akkdong/Vario-STM32/case/Button.png

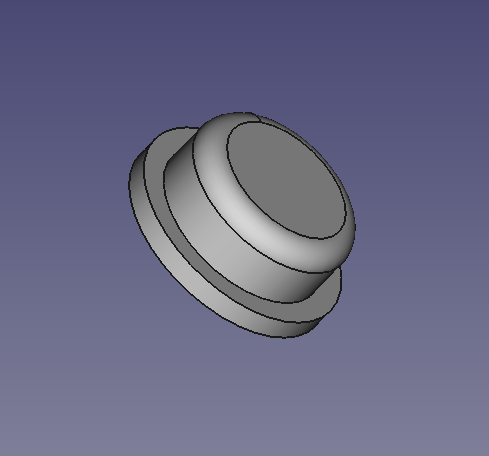
case/Button.png
