akkdong/Vario-STM32/case/case-bottom.png

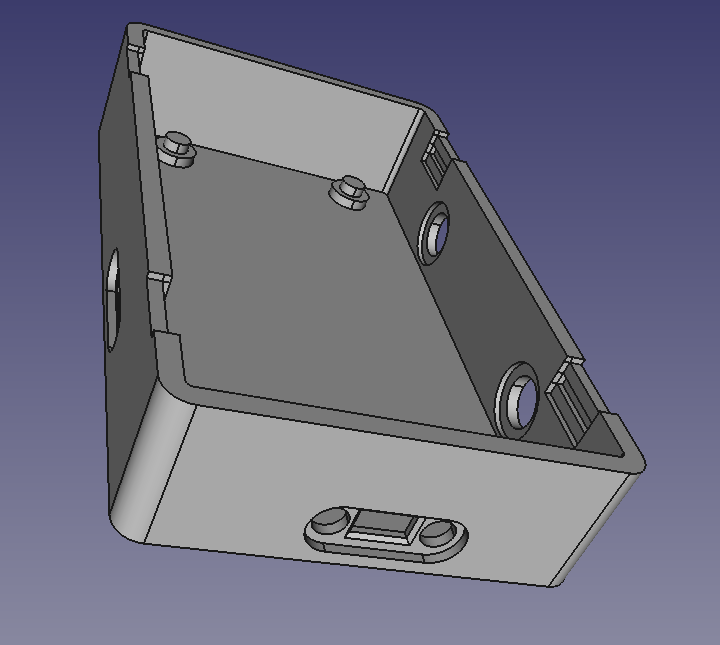
case/case-bottom.png
