akkdong/Vario-STM32/case/case-top.png

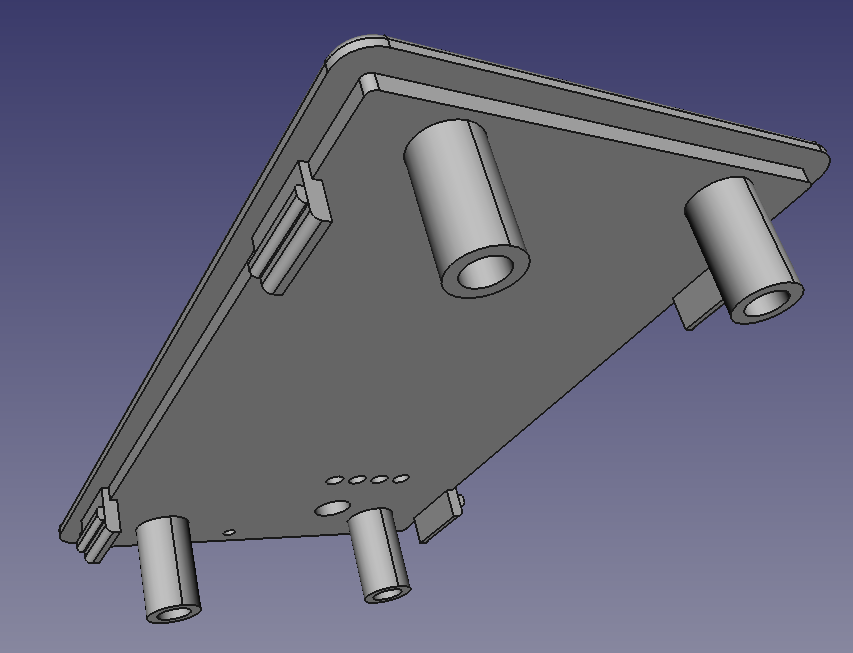
case/case-top.png
