akkdong/Vario-STM32/doc/auto power off - 2.jpg

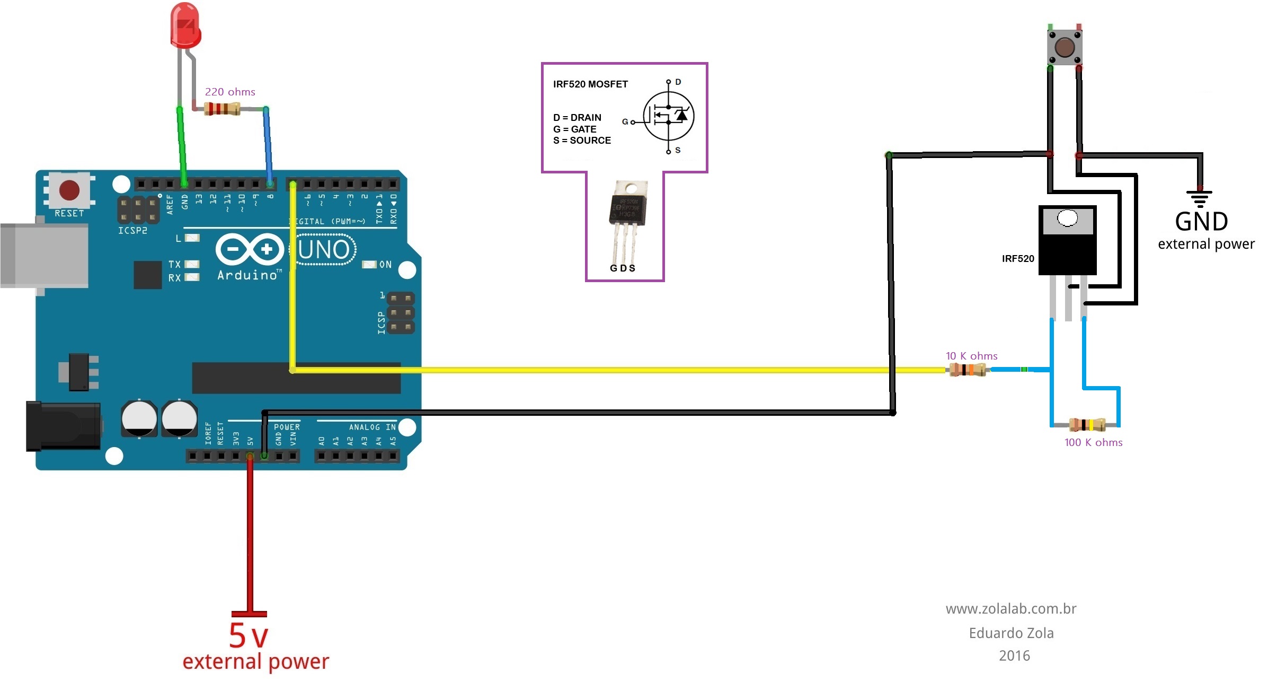
doc/auto power off - 2.jpg
