akkdong/Vario-STM32/doc/auto power off - 3.jpg

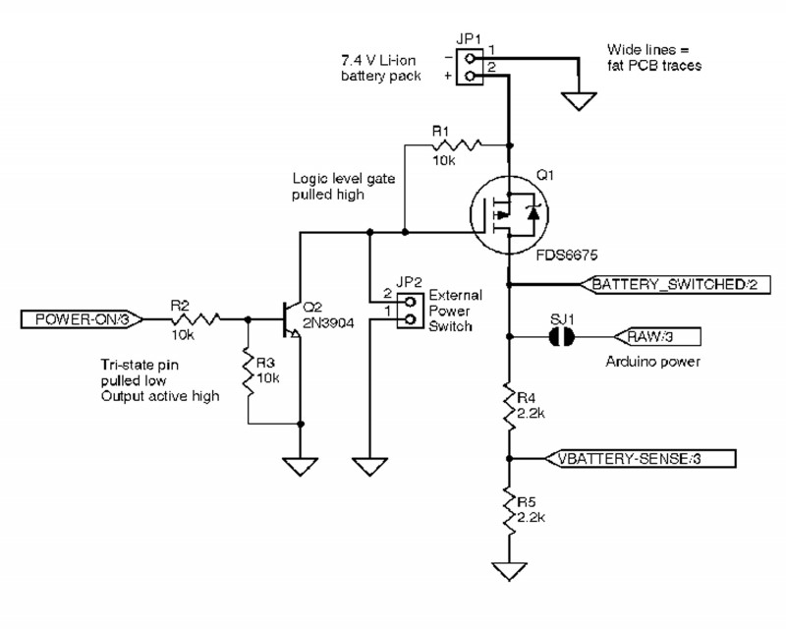
doc/auto power off - 3.jpg
