akkdong/Vario-STM32/doc/FGPMMOPA6C.jpg

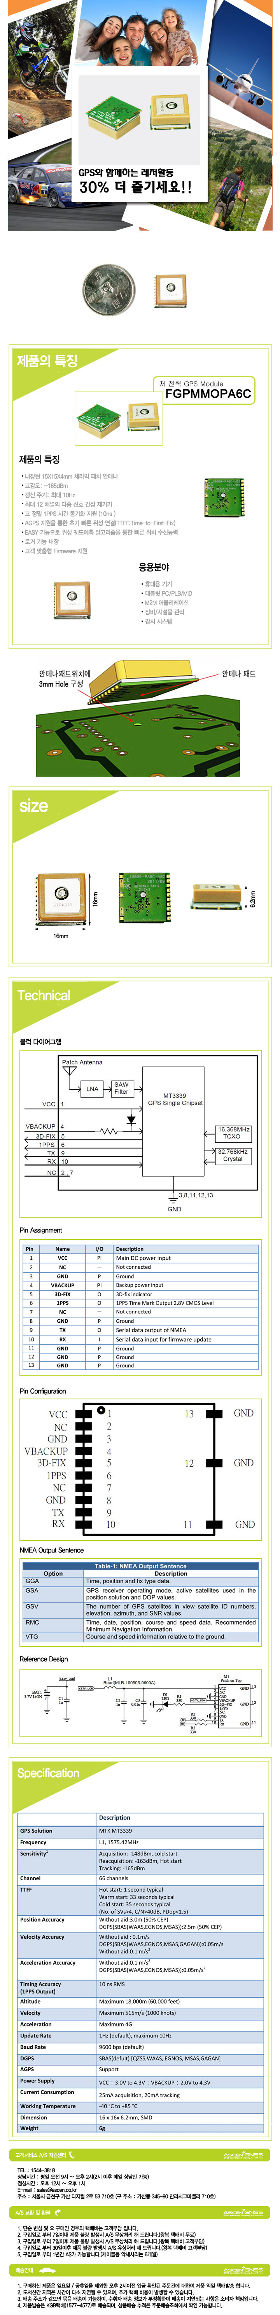
doc/FGPMMOPA6C.jpg
