akkdong/Vario-STM32/doc/in-rush-limited-push-button-on-off-toggle-power-switch-circuit.png

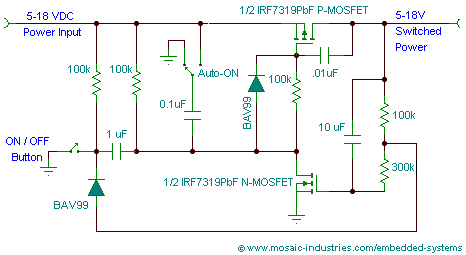
doc/in-rush-limited-push-button-on-off-toggle-power-switch-circuit.png
