akkdong/Vario-STM32/doc/latching-high-side-toggle-switch-circuit-for-capacitive-loads.png

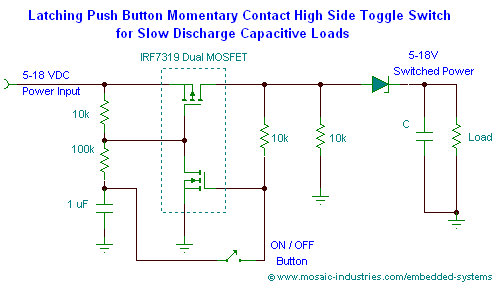
doc/latching-high-side-toggle-switch-circuit-for-capacitive-loads.png
