akkdong/Vario-STM32/doc/LTC2950-1 - Push Button OnOff Controller.png

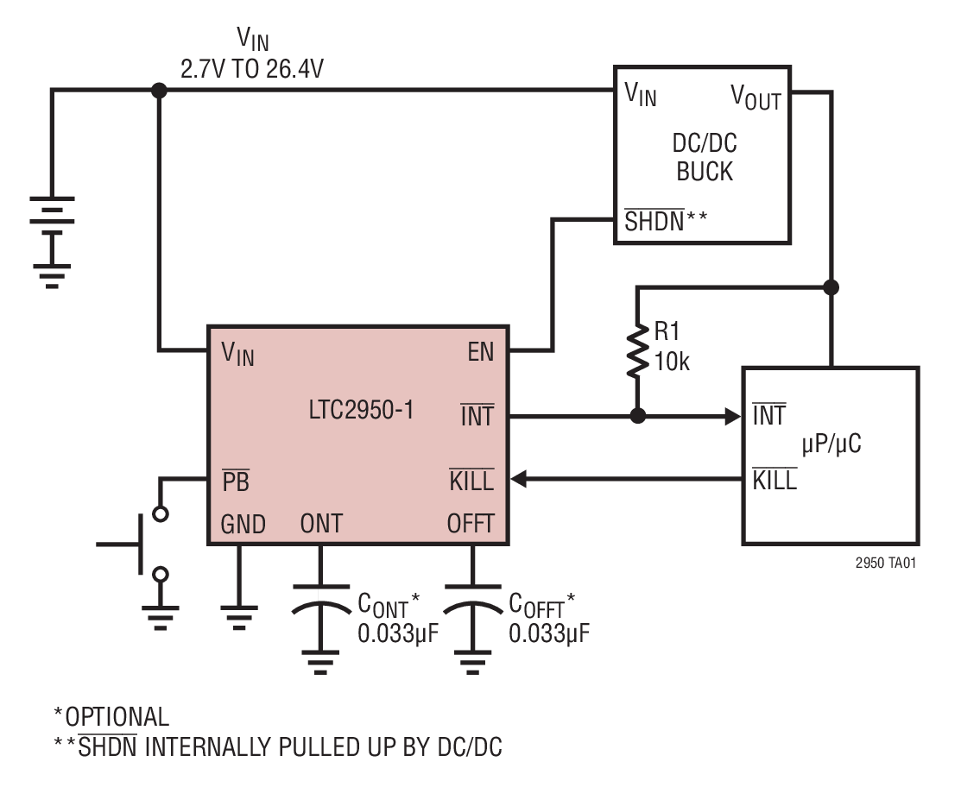
doc/LTC2950-1 - Push Button OnOff Controller.png
