akkdong/Vario-STM32/doc/LTC2953 - Push Button OnOff Controller with Voltage Monitoring.png

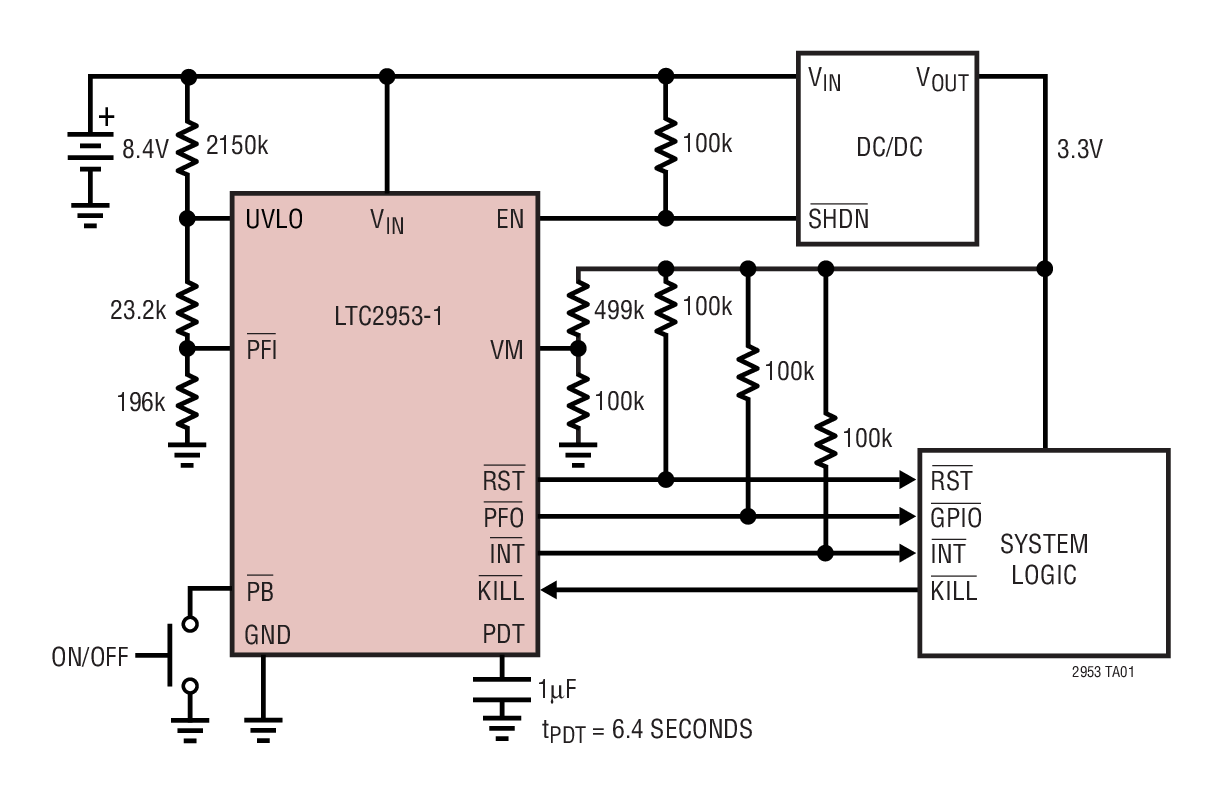
doc/LTC2953 - Push Button OnOff Controller with Voltage Monitoring.png
