akkdong/Vario-STM32/doc/pcb/pcb-bottom-rev2.png

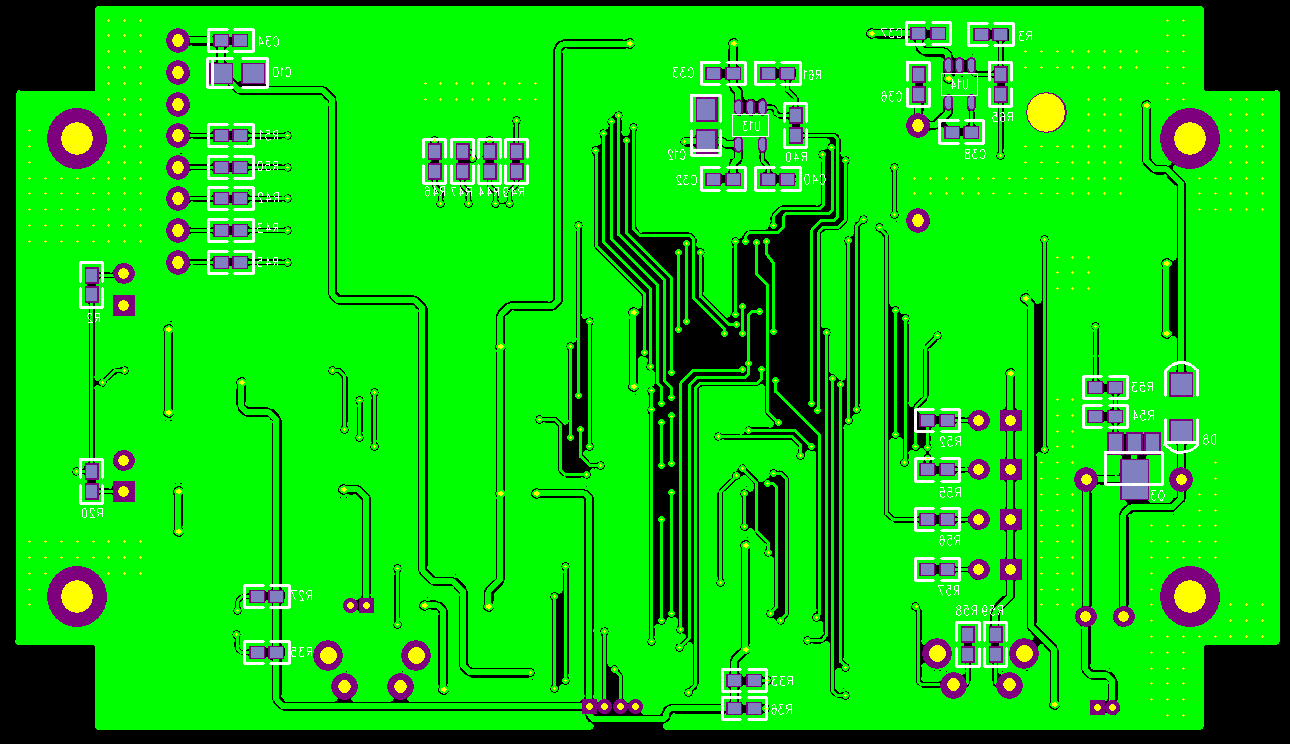
doc/pcb/pcb-bottom-rev2.png
