akkdong/Vario-STM32/doc/pcb/pcb-bottom.png

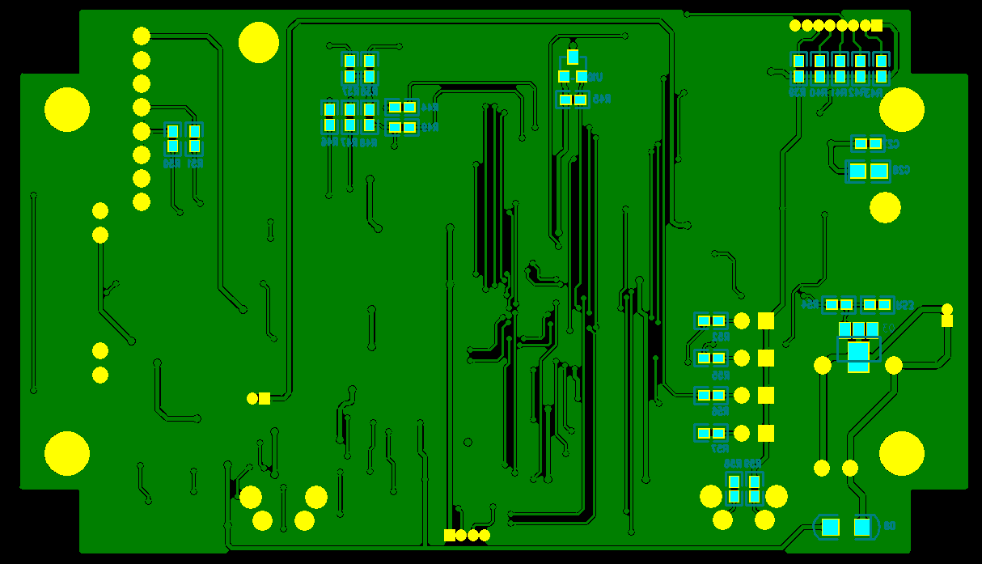
doc/pcb/pcb-bottom.png
