akkdong/Vario-STM32/doc/pcb/pcb-top.png

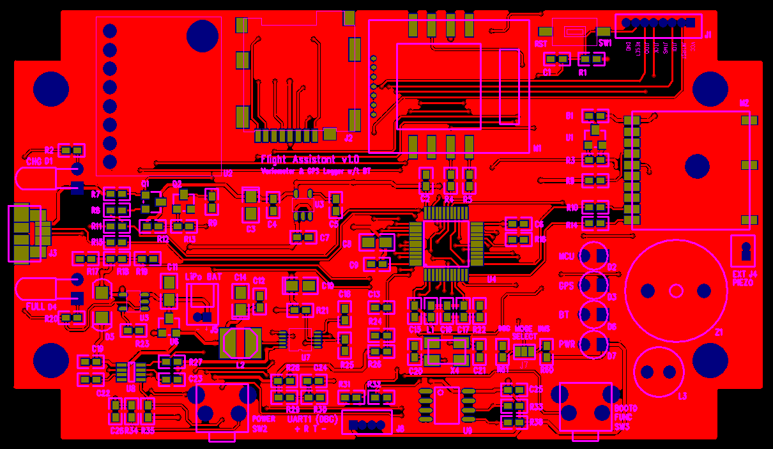
doc/pcb/pcb-top.png
