akkdong/Vario-STM32/doc/piezo/alarm-module.png

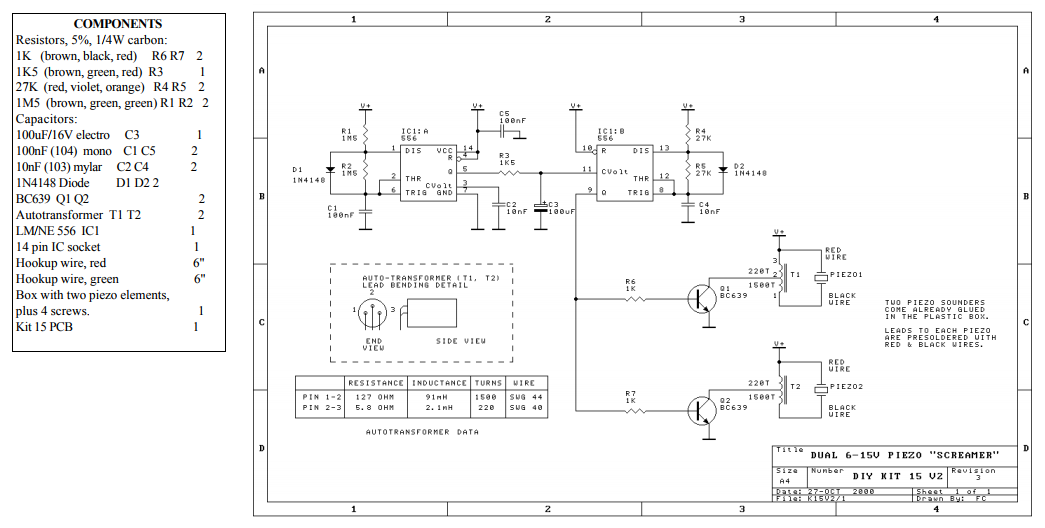
doc/piezo/alarm-module.png
