akkdong/Vario-STM32/doc/piezo/Dual Piezo Driver.png

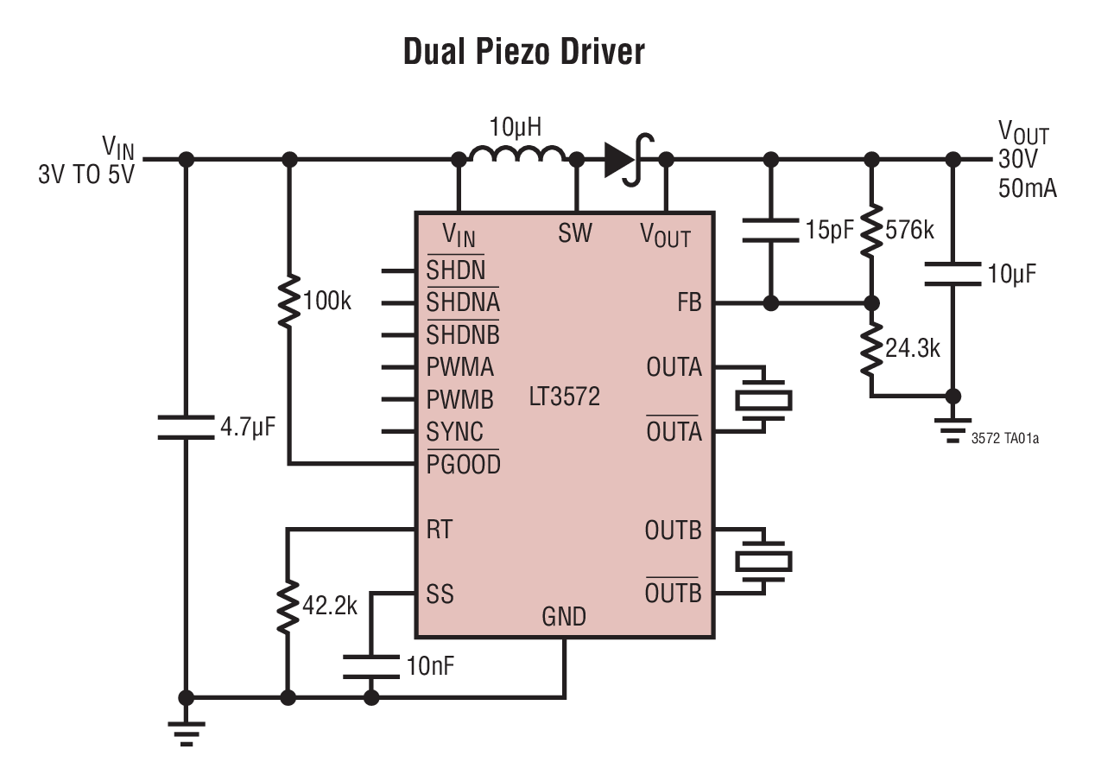
doc/piezo/Dual Piezo Driver.png
