akkdong/Vario-STM32/doc/piezo/FEFHRLSHNM44L13.MEDIUM.jpg

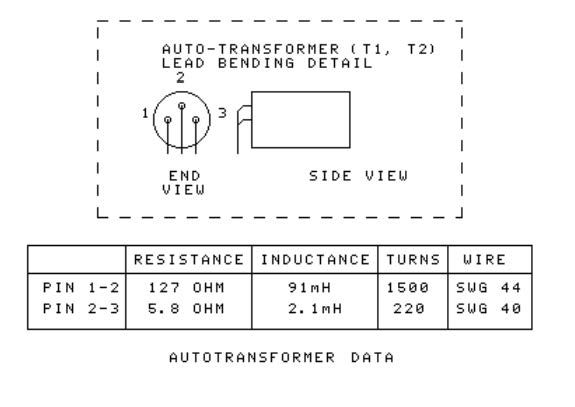
doc/piezo/FEFHRLSHNM44L13.MEDIUM.jpg
