akkdong/Vario-STM32/doc/piezo/FS6PPDVHNM44D6V.MEDIUM.jpg

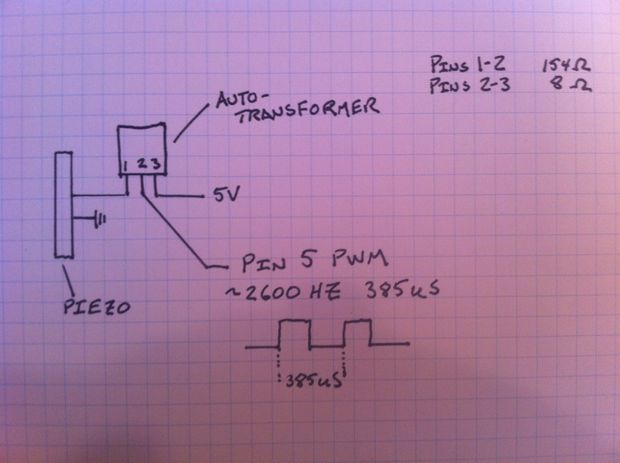
doc/piezo/FS6PPDVHNM44D6V.MEDIUM.jpg
