akkdong/Vario-STM32/doc/piezo/sweeping tone alarm beeper.jpg

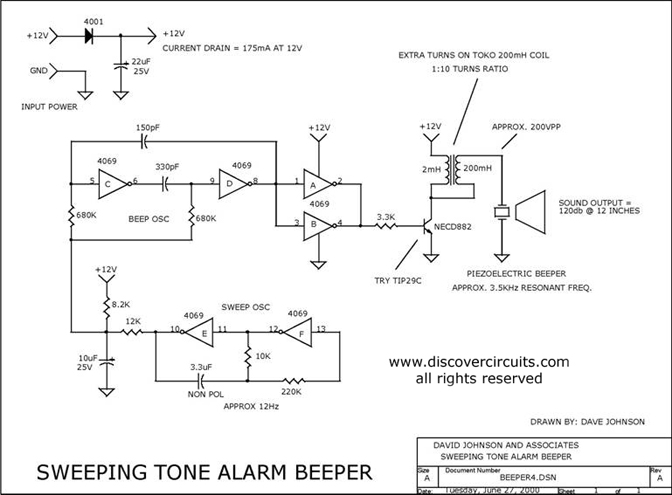
doc/piezo/sweeping tone alarm beeper.jpg
