akkdong/Vario-STM32/case/Sample-Case.FCStd

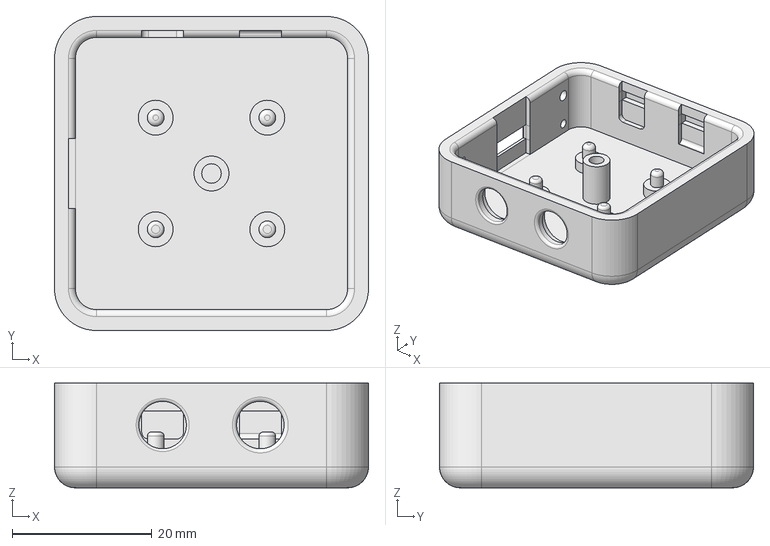
[picture p39: CAD file, 2018-11-01]
case/Sample-Case.FCStd
45.0 x 45.0 x 15.0 mm
