akkdong/Vario-STM32/case/Case-Button.stl

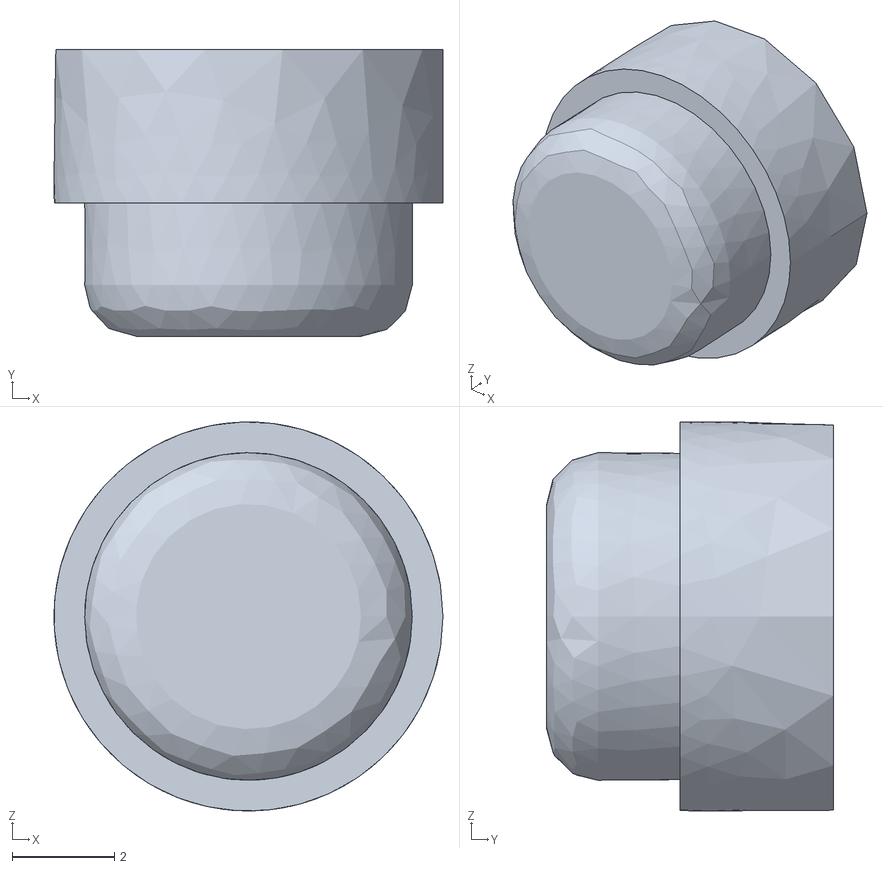
[picture p40: CAD file, 2018-10-25]
case/Case-Button.stl
7.60 x 5.60 x 7.60
