akkdong/Vario-STM32/case/Case-Top-2.FCStd

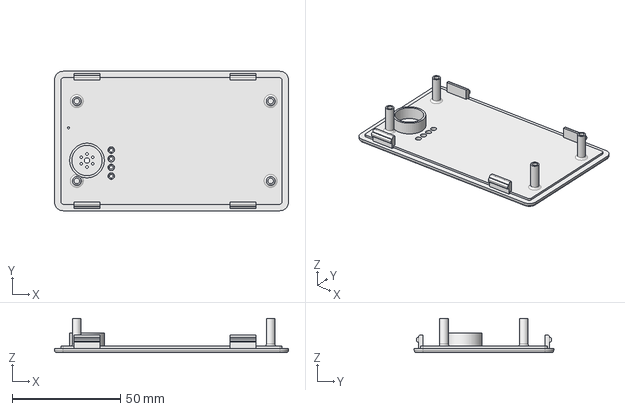
[picture p41: CAD file, 2018-10-23]
case/Case-Top-2.FCStd
108.0 x 64.4 x 15.8 mm
