akkdong/Vario-STM32/case/Case-Bottom-2.FCStd

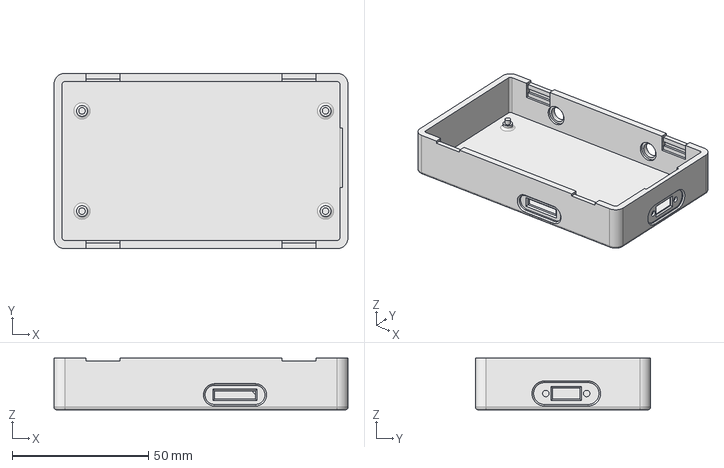
[picture p42: CAD file, 2018-10-23]
case/Case-Bottom-2.FCStd
108.0 x 64.4 x 19.0 mm
