akkdong/Vario-STM32/case/Button.FCStd

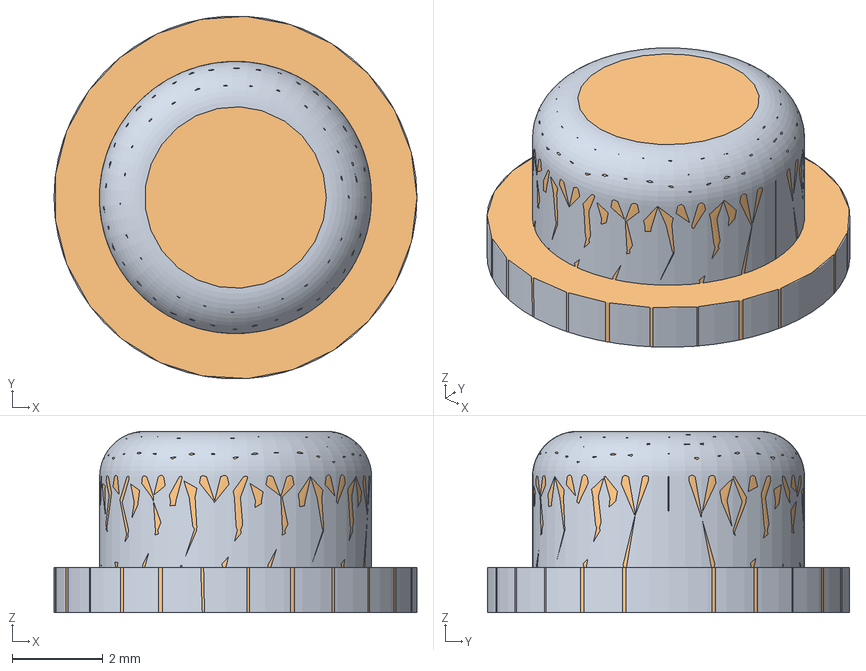
[picture p43: CAD file, 2018-10-23]
case/Button.FCStd
8.00 x 7.99 x 4.00 mm
Pocket (Meshed)
