akkdong/Vario-STM32/case/Case-Bottom.FCStd

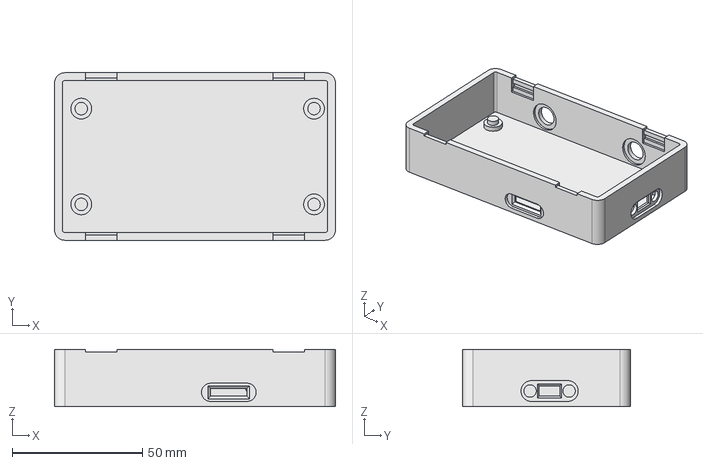
[picture p44: CAD file, 2018-10-21]
case/Case-Bottom.FCStd
108.0 x 64.4 x 22.0 mm
