akkdong/Vario-STM32/doc/battery voltage measure example.jpg

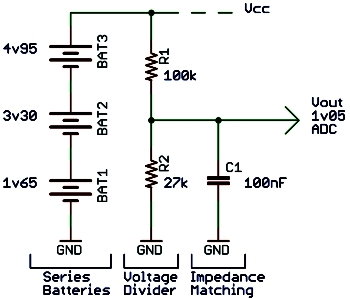
doc/battery voltage measure example.jpg
