akkdong/Vario-STM32/pads/Variometer-STM32-Rev2.pdf

D

6 | 5 | 4 | 3 | 2 | 1

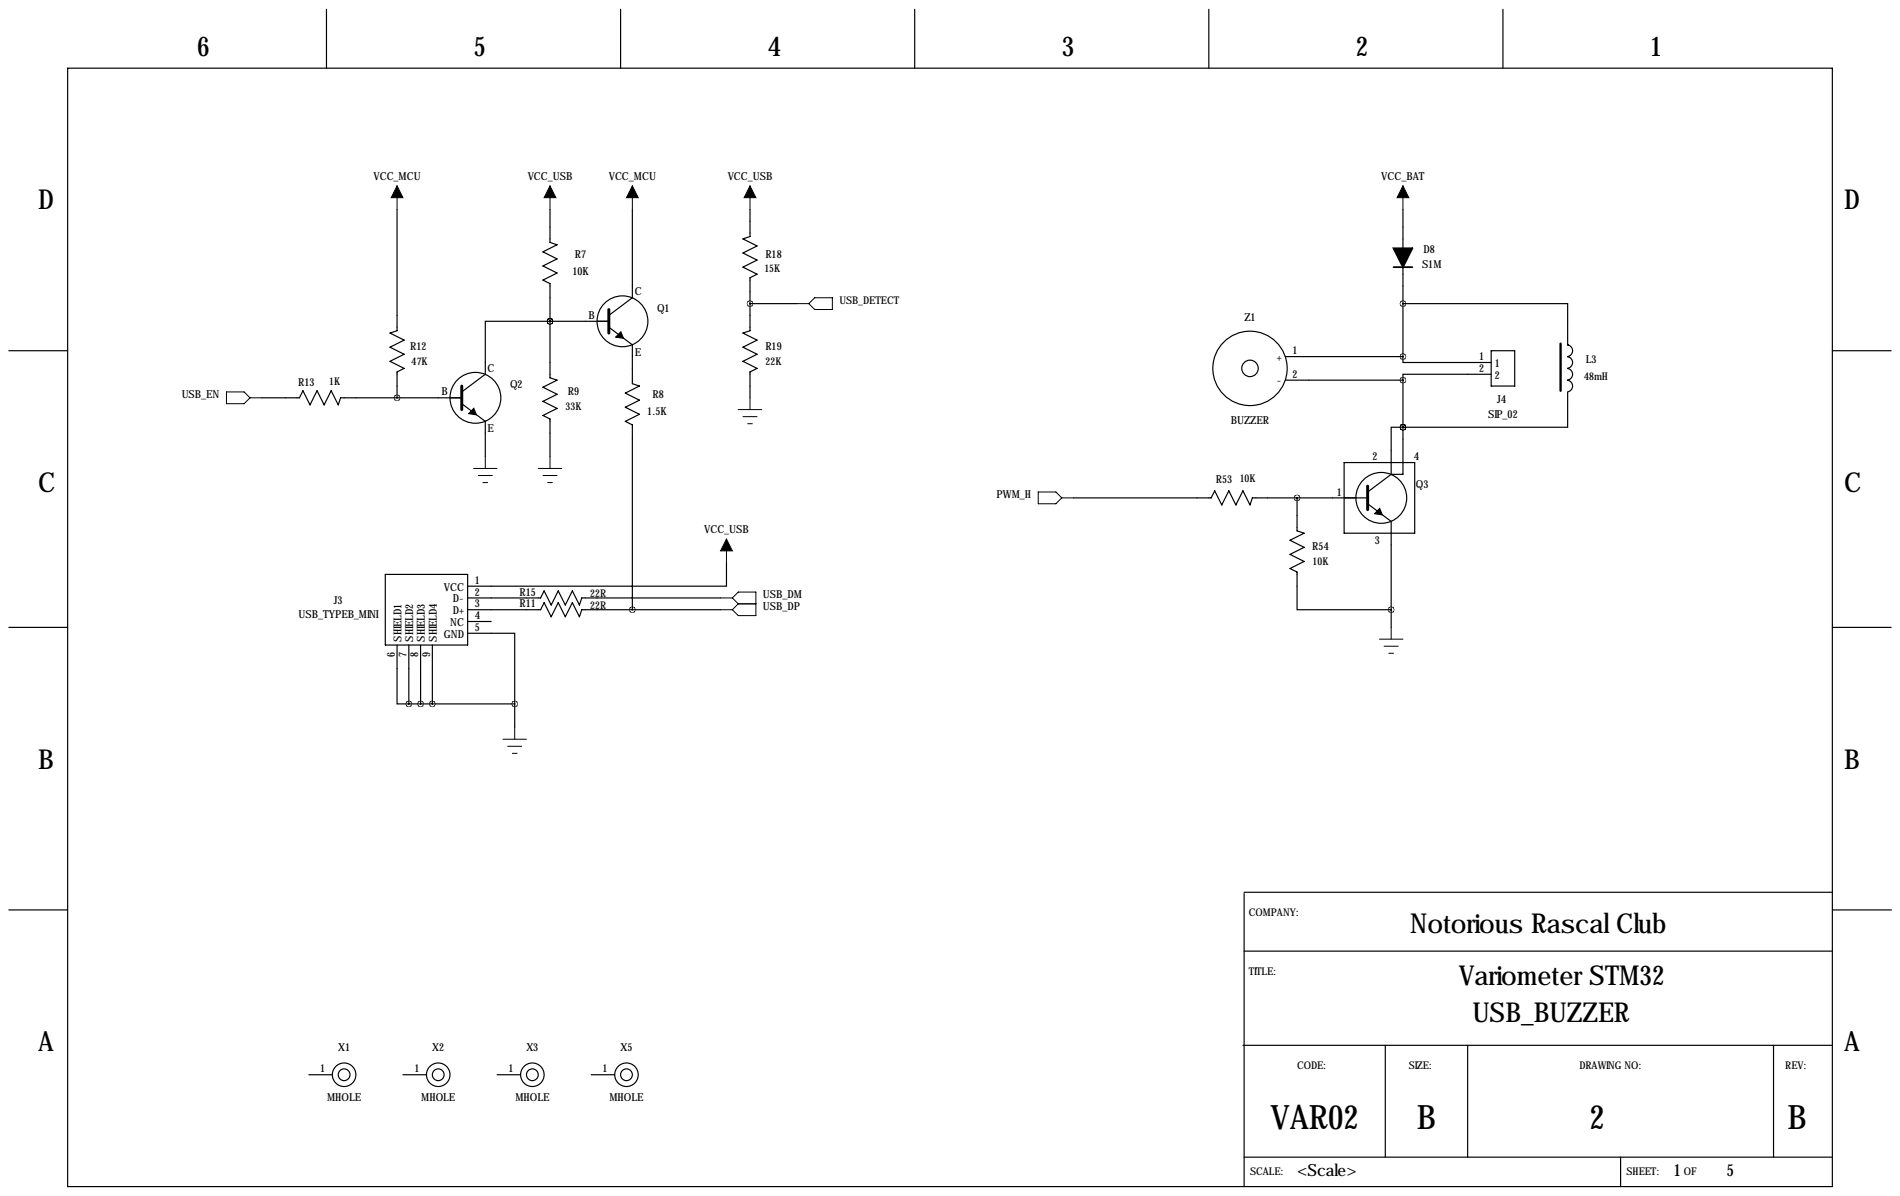
[picture p58: page 1]

CODE: VAR02 | SIZE: B | DRAWING NO: 2 | REV: B

<Scale> SCALE: | 1 5 SHEET: OF

D

D

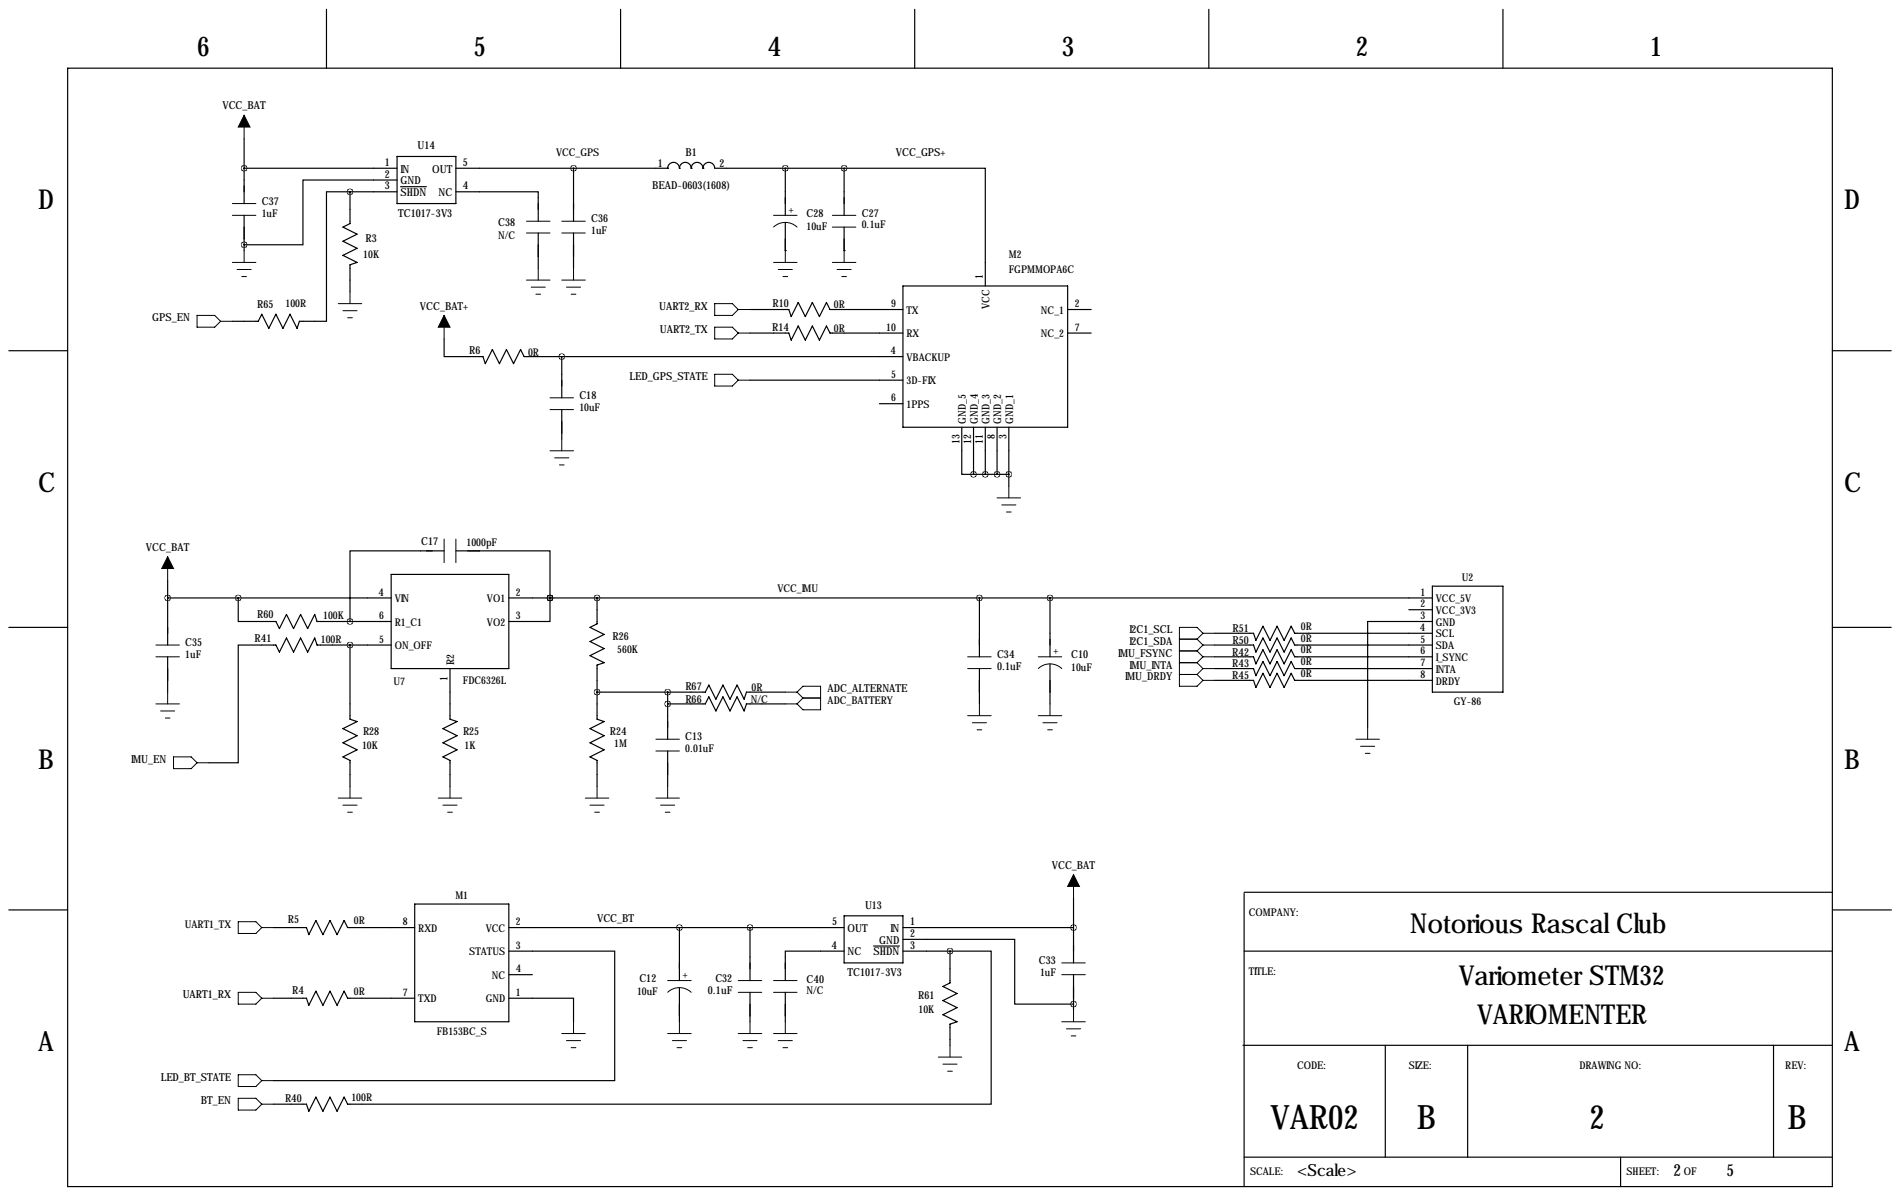
[picture p59: page 2]

CODE: VAR02 | SIZE: B | DRAWING NO: 2 | REV: B

<Scale> | 2 5

D

D

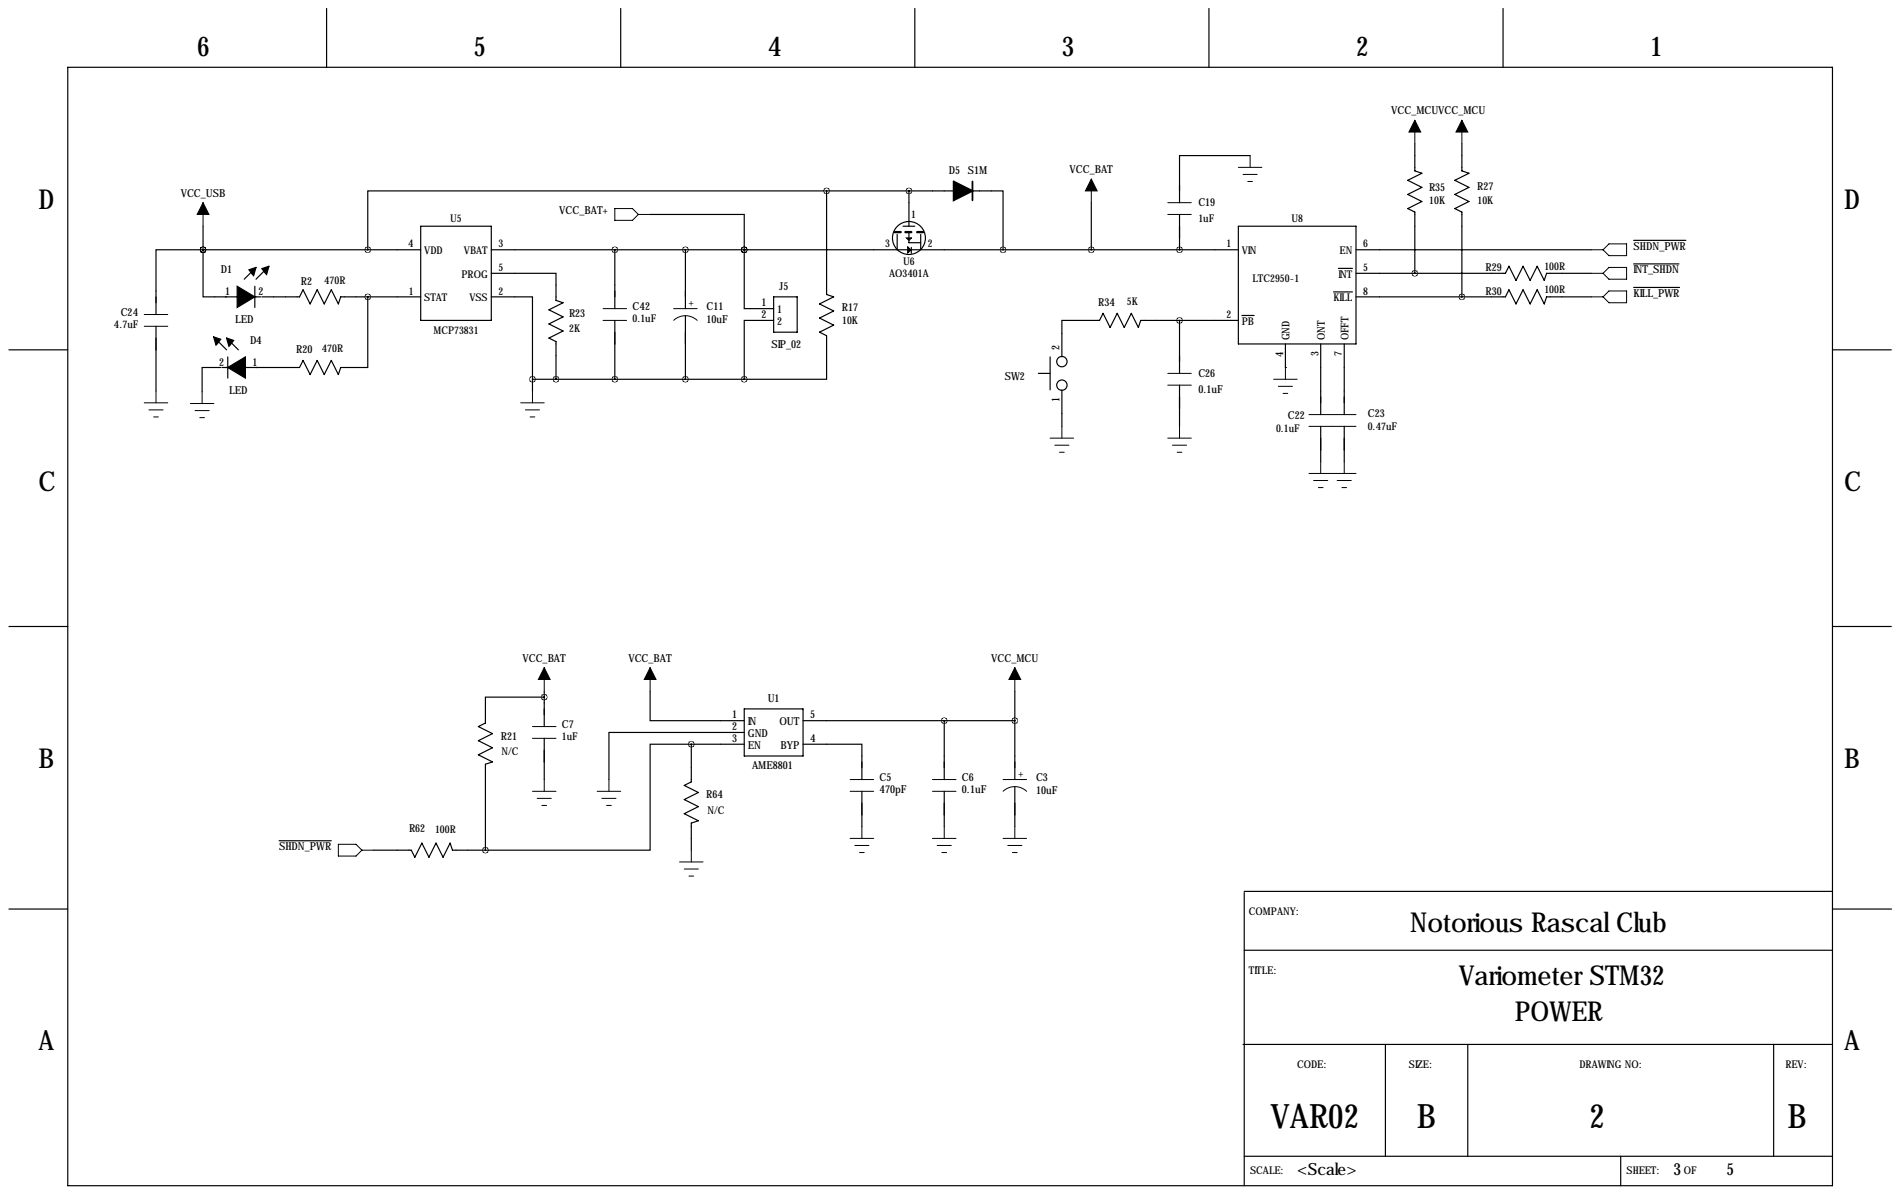
[picture p60: page 3]

VCC_MCUVCC_MCU

CODE: VAR02 | SIZE: B | DRAWING NO: 2 | REV: B

<Scale> | 3 5

D

D

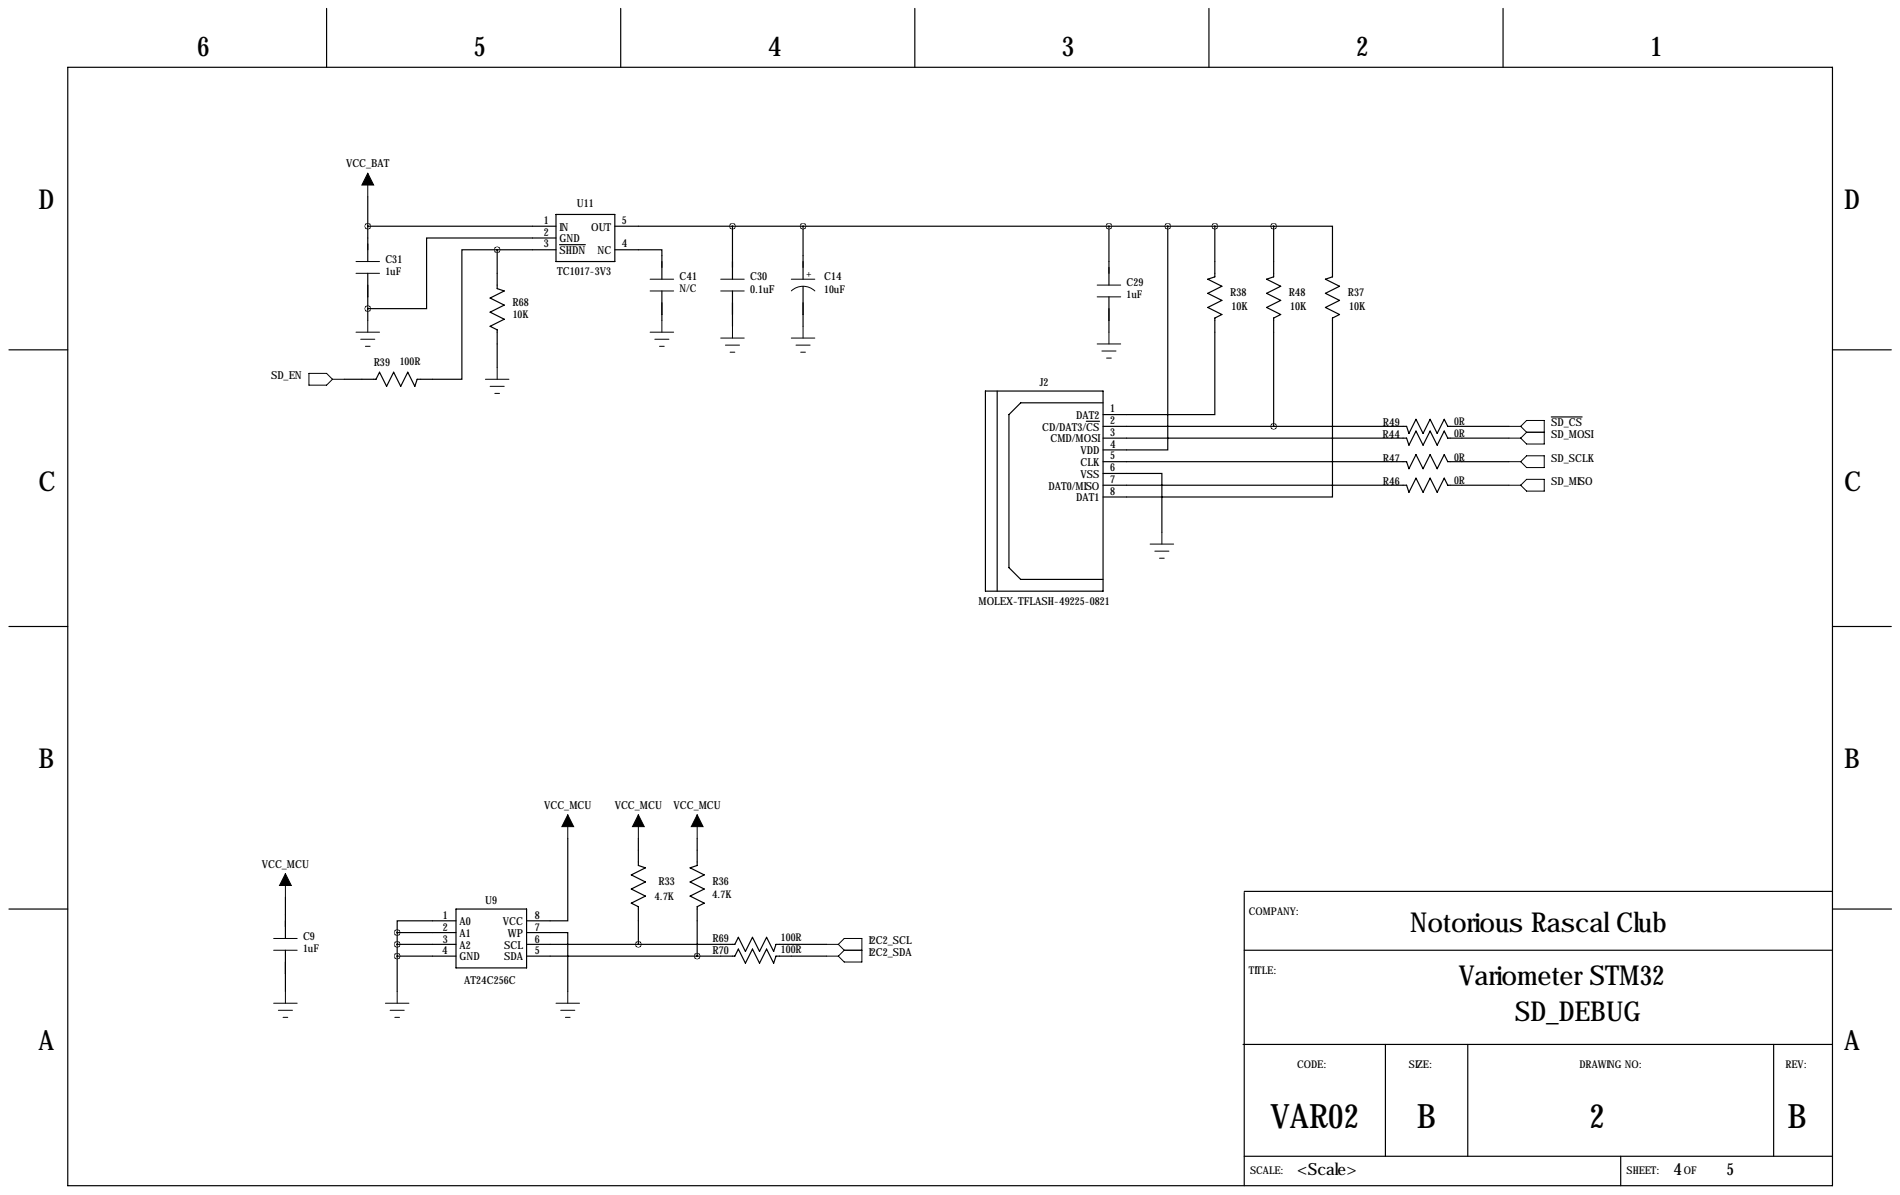
[picture p61: page 4]

CODE: VAR02 | SIZE: B | DRAWING NO: 2 | REV: B

<Scale> | 4 5

D

D

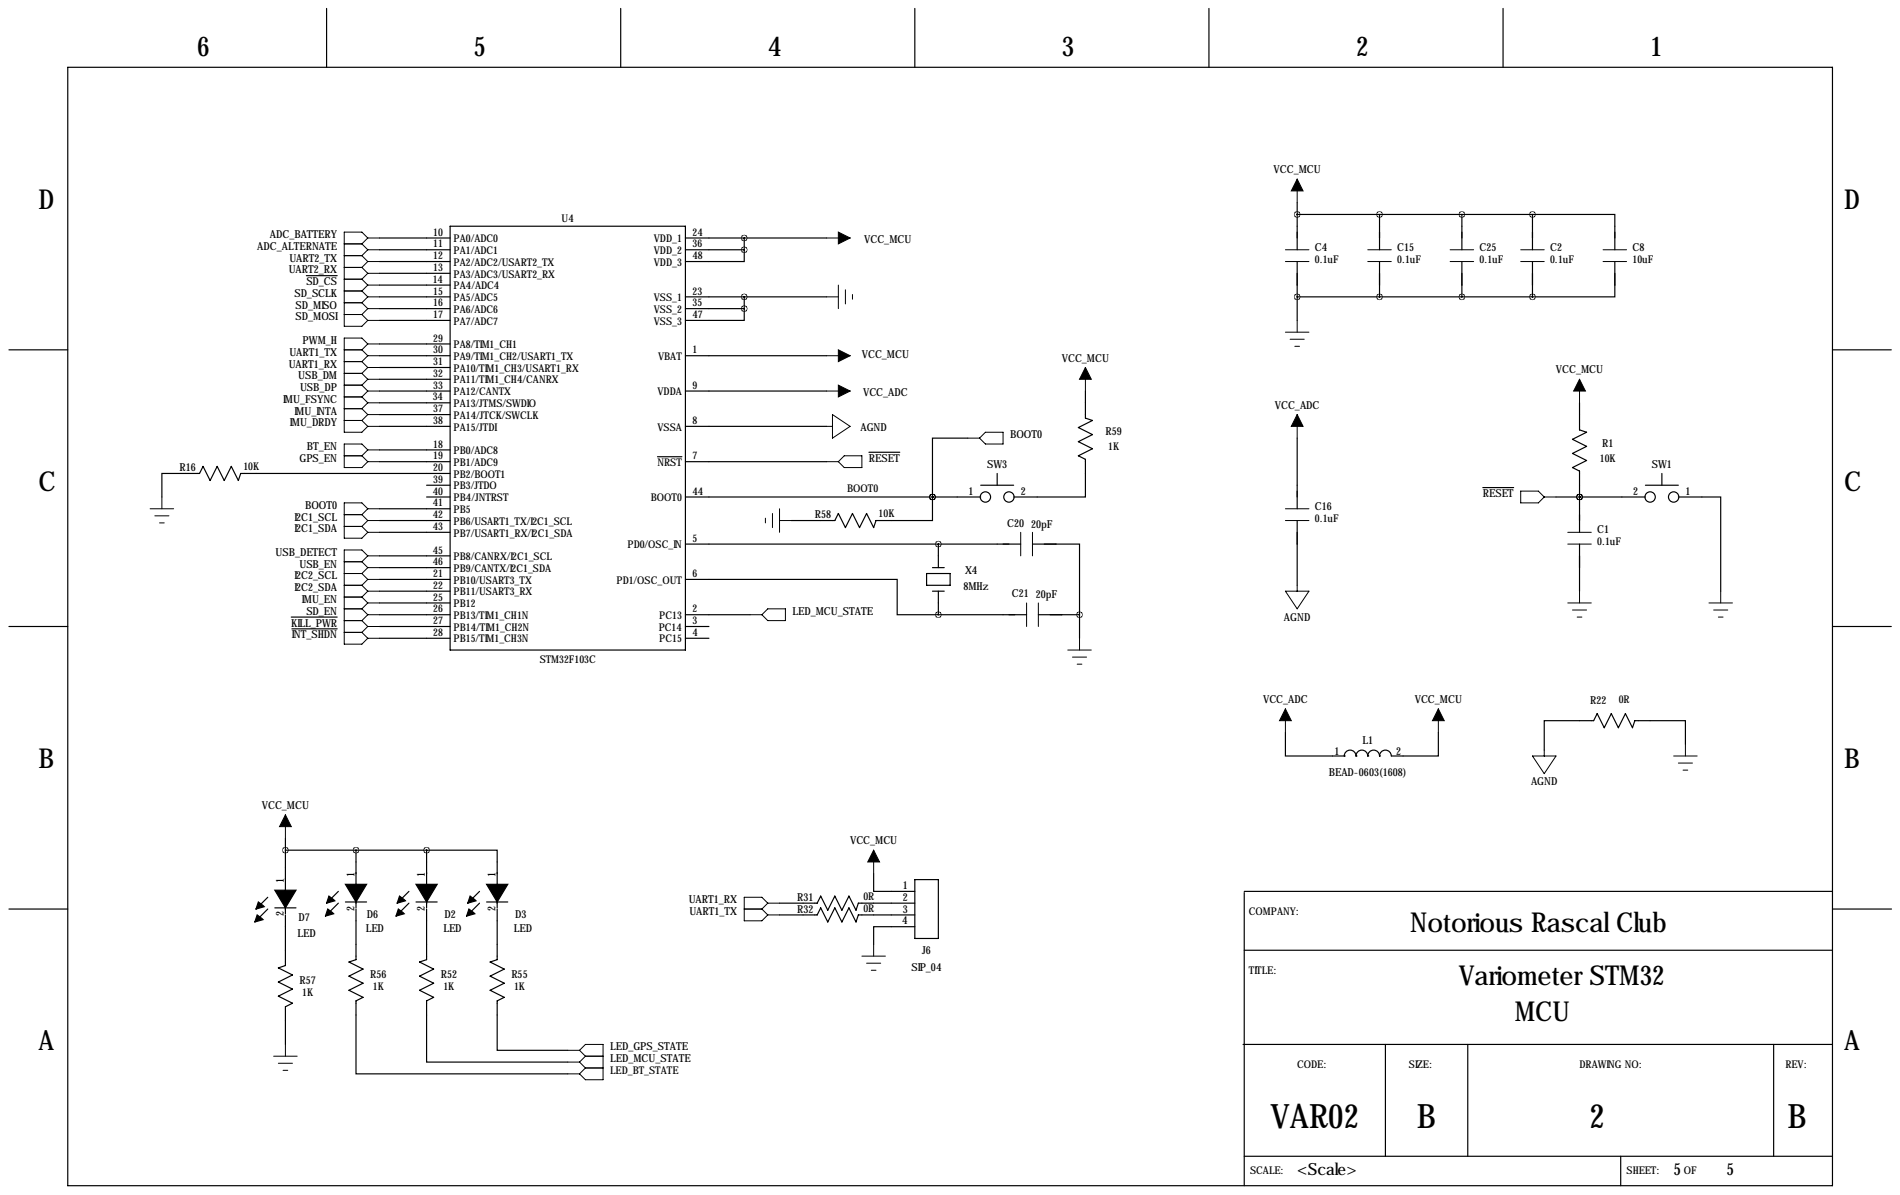
[picture p62: page 5]

CODE: VAR02 | SIZE: B | DRAWING NO: 2 | REV: B

<Scale> | 5 5
