akkdong/Vario-STM32/doc/8-KLT-1105VSMT.pdf

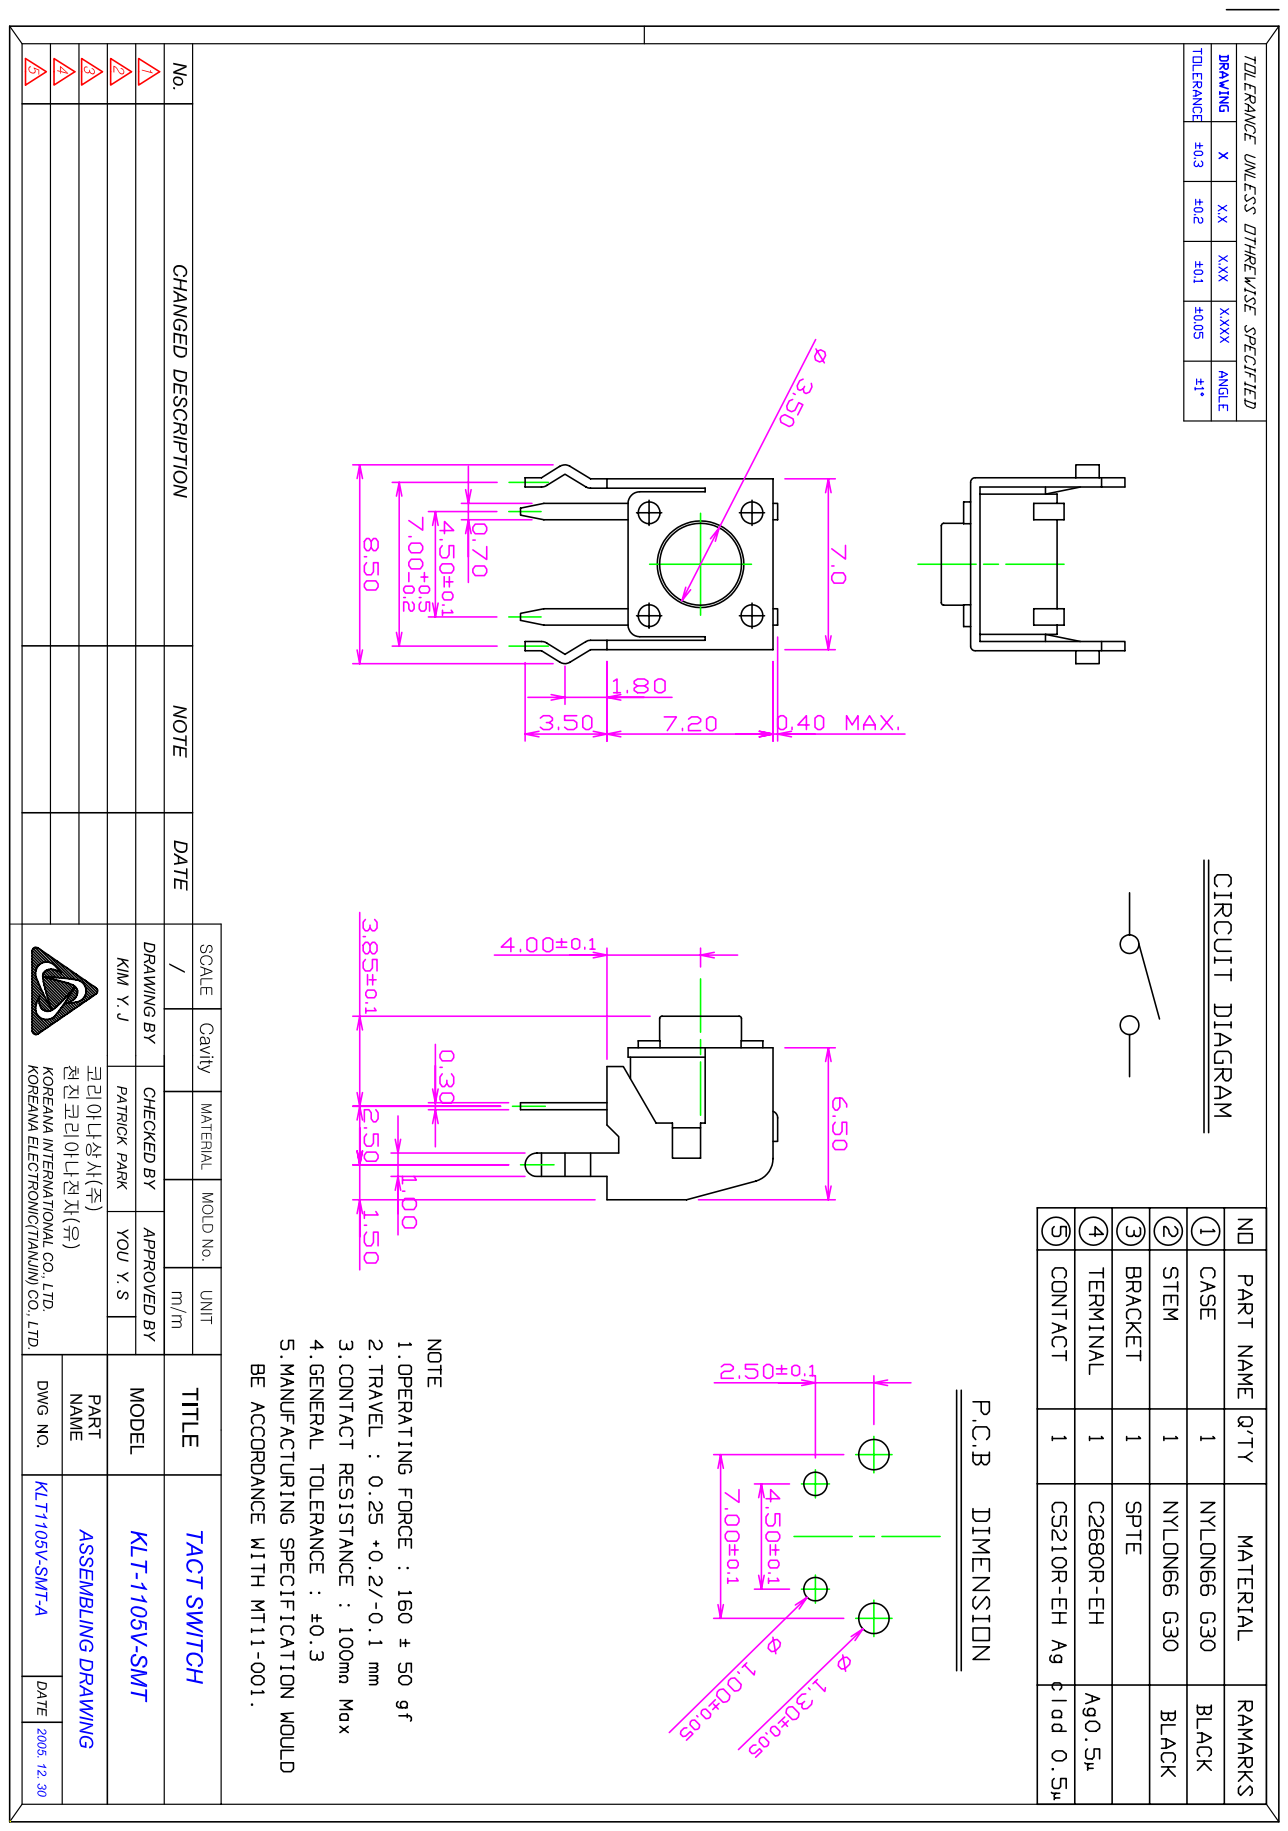
[picture p63: page 1]
