akkdong/Vario-STM32/doc/mpb401.pdf

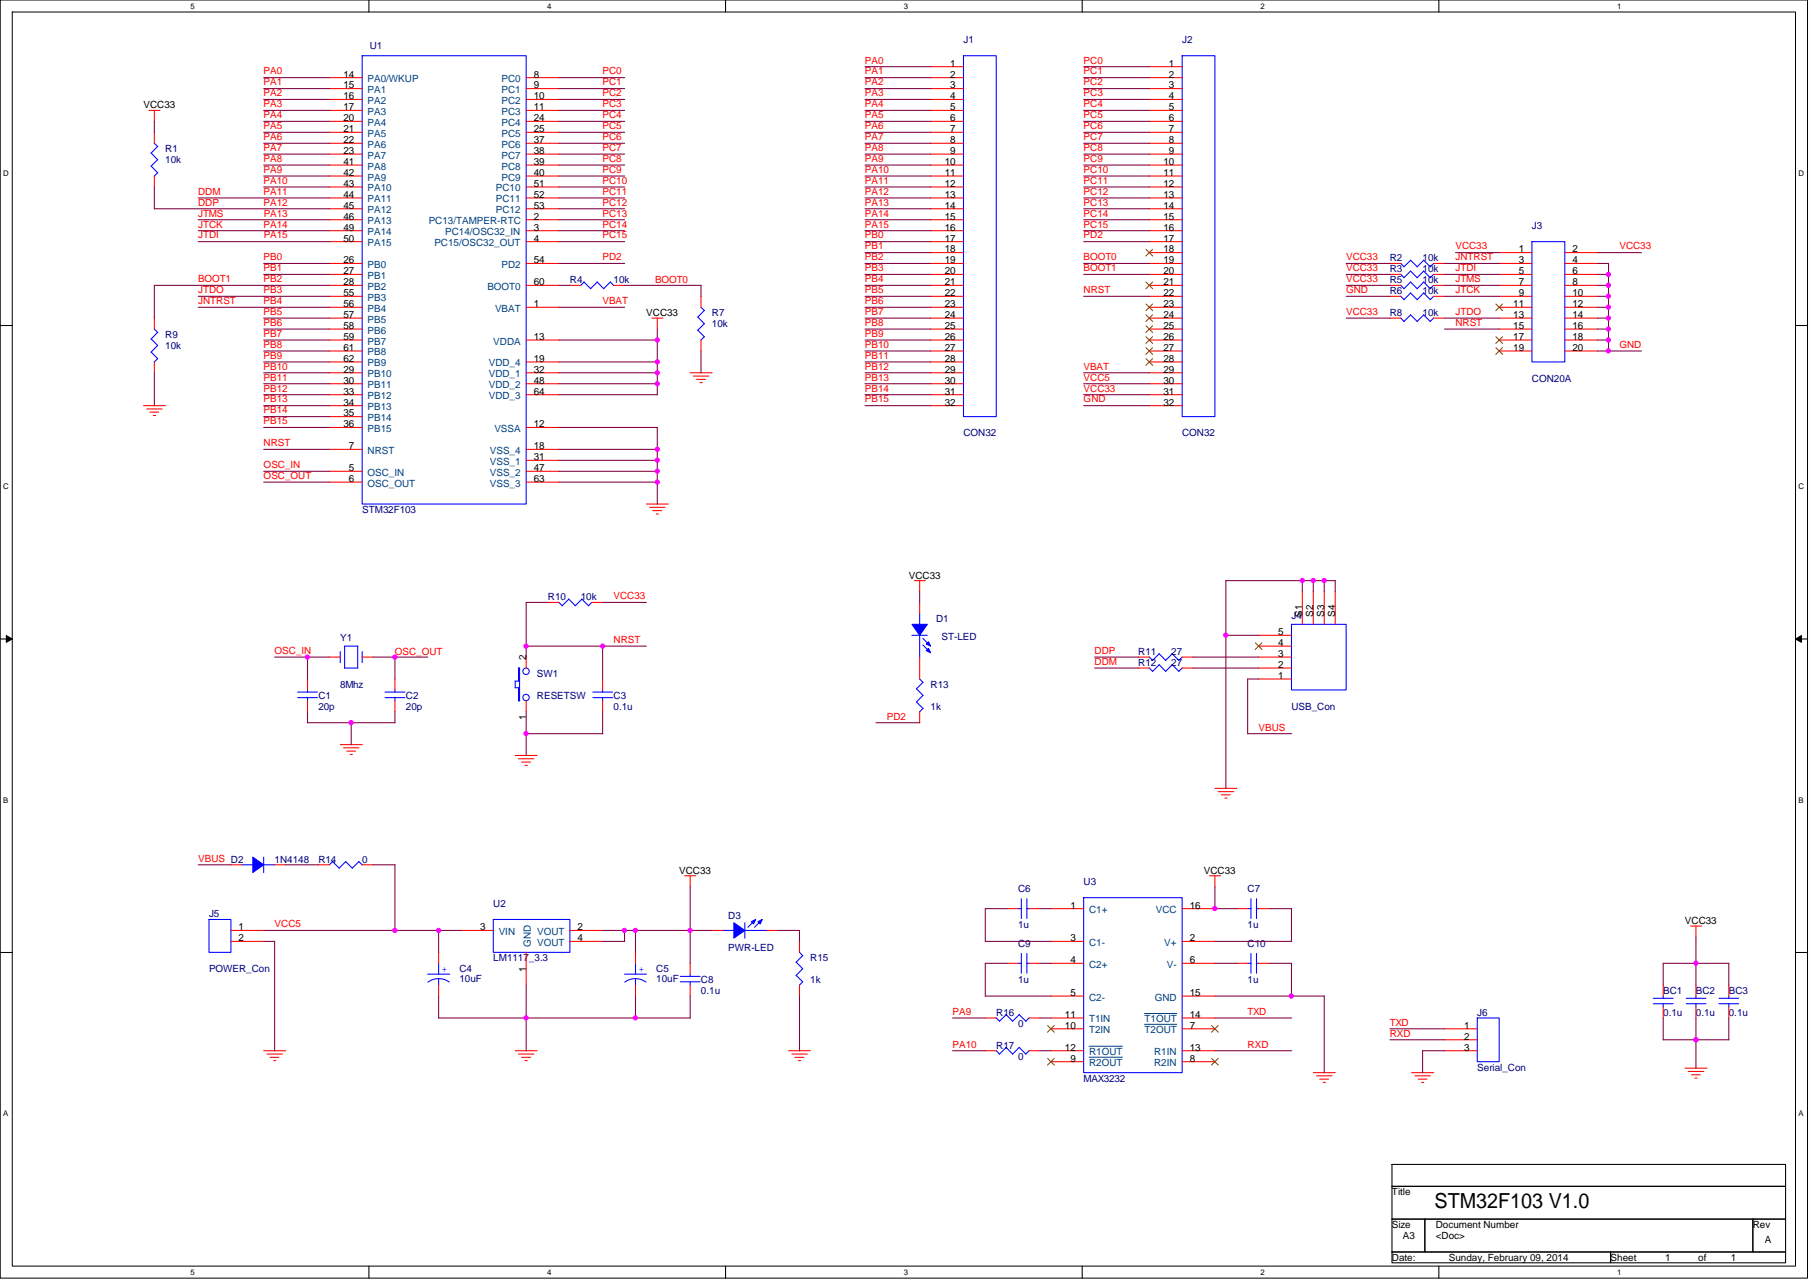
[picture p64: page 1]
