akkdong/Vario-STM32/doc/BC04-B/BLK-MD-BC04-B_DEMO.pdf

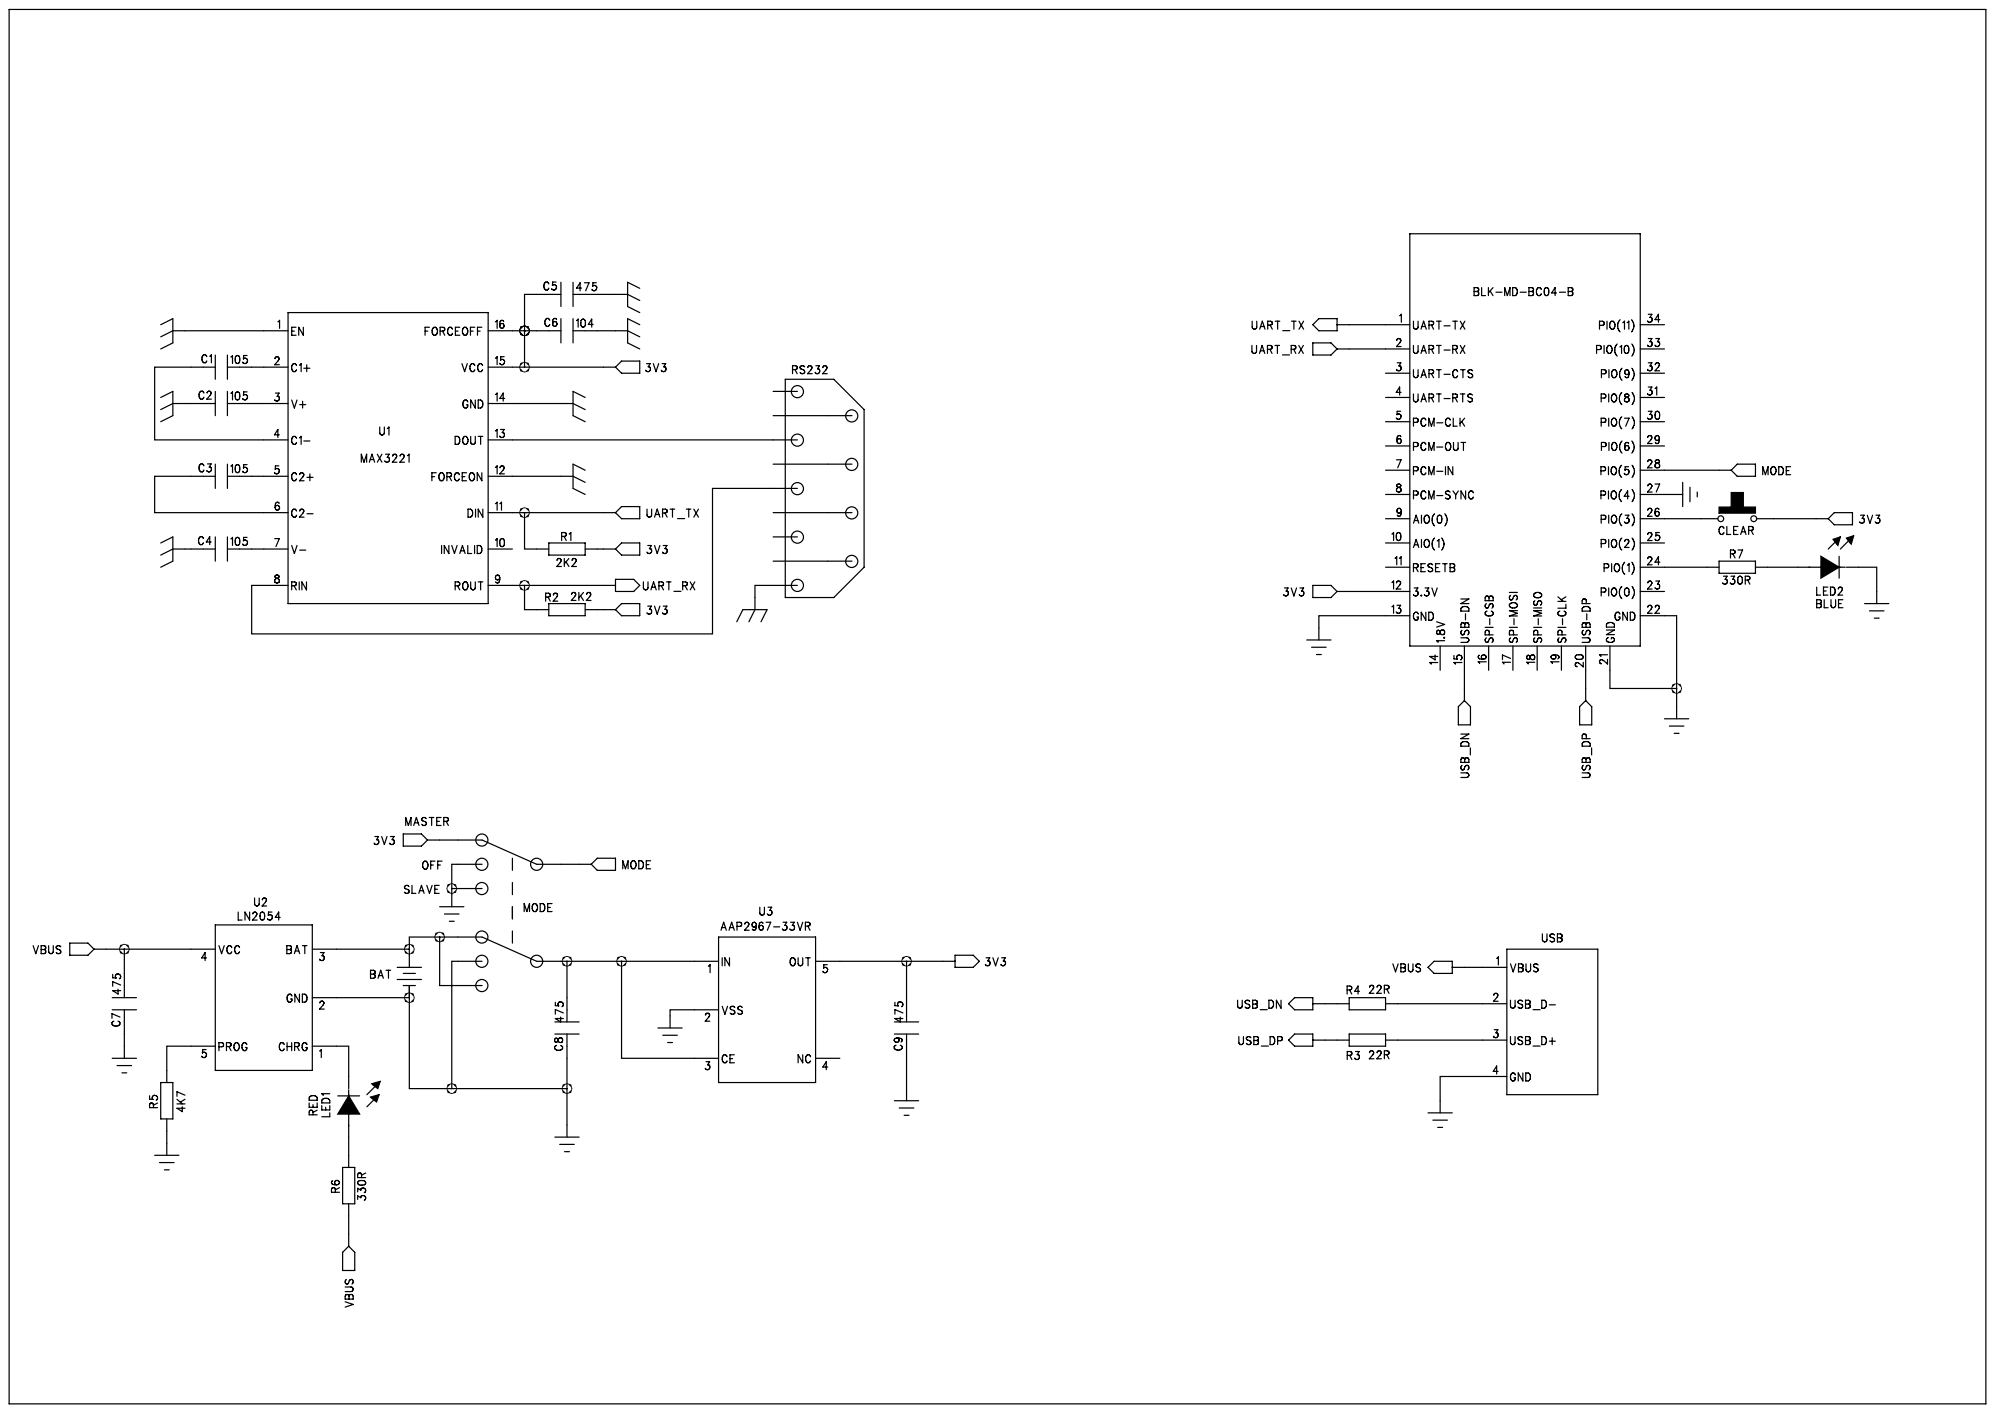
[picture p65: page 1]
