akkdong/Vario-STM32/pads/Variometer-STM32-Rev1.pdf

D

6 | 5 | 4 | 3 | 2 | 1

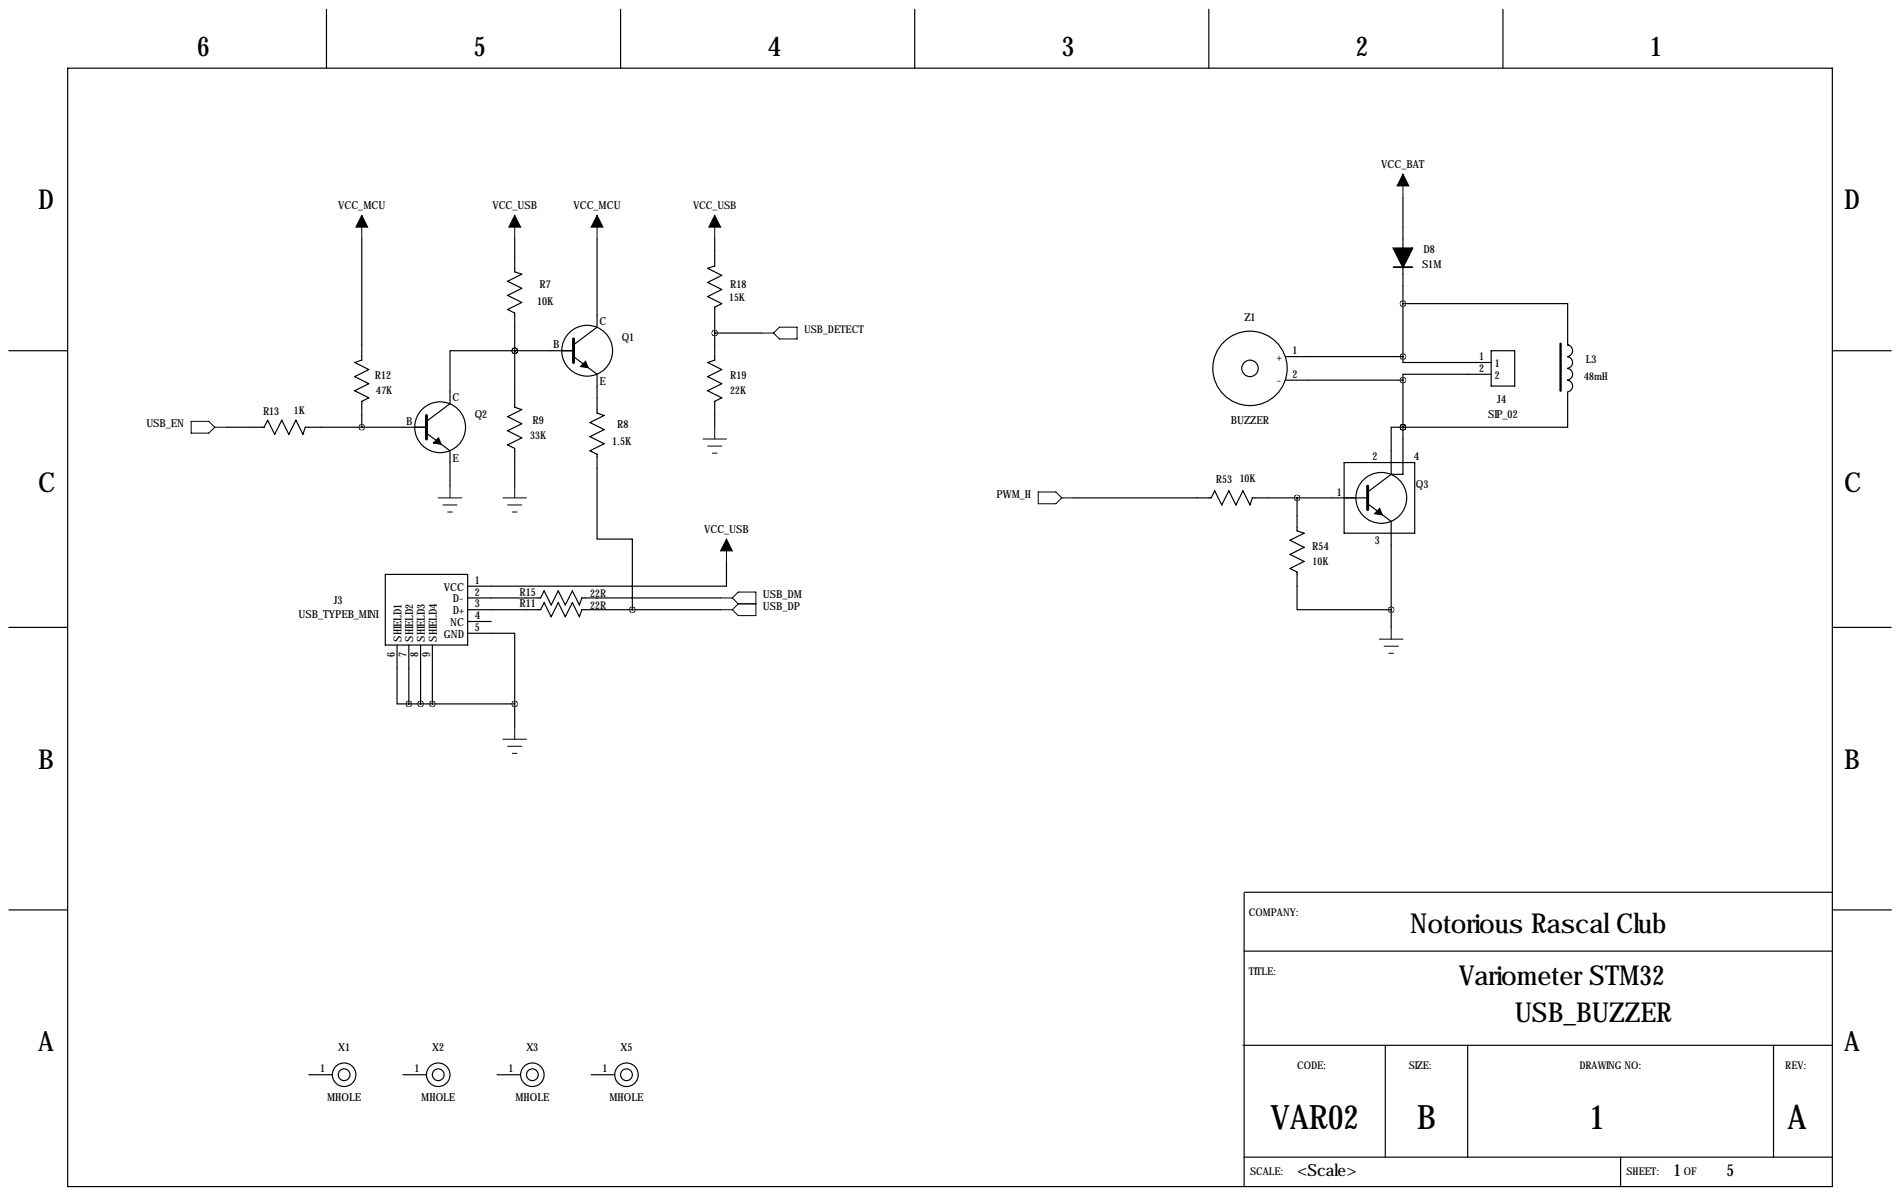
[picture p66: page 1]

CODE: VAR02 | SIZE: B | DRAWING NO: 1 | REV: A

<Scale> SCALE: | 1 5 SHEET: OF

D

D

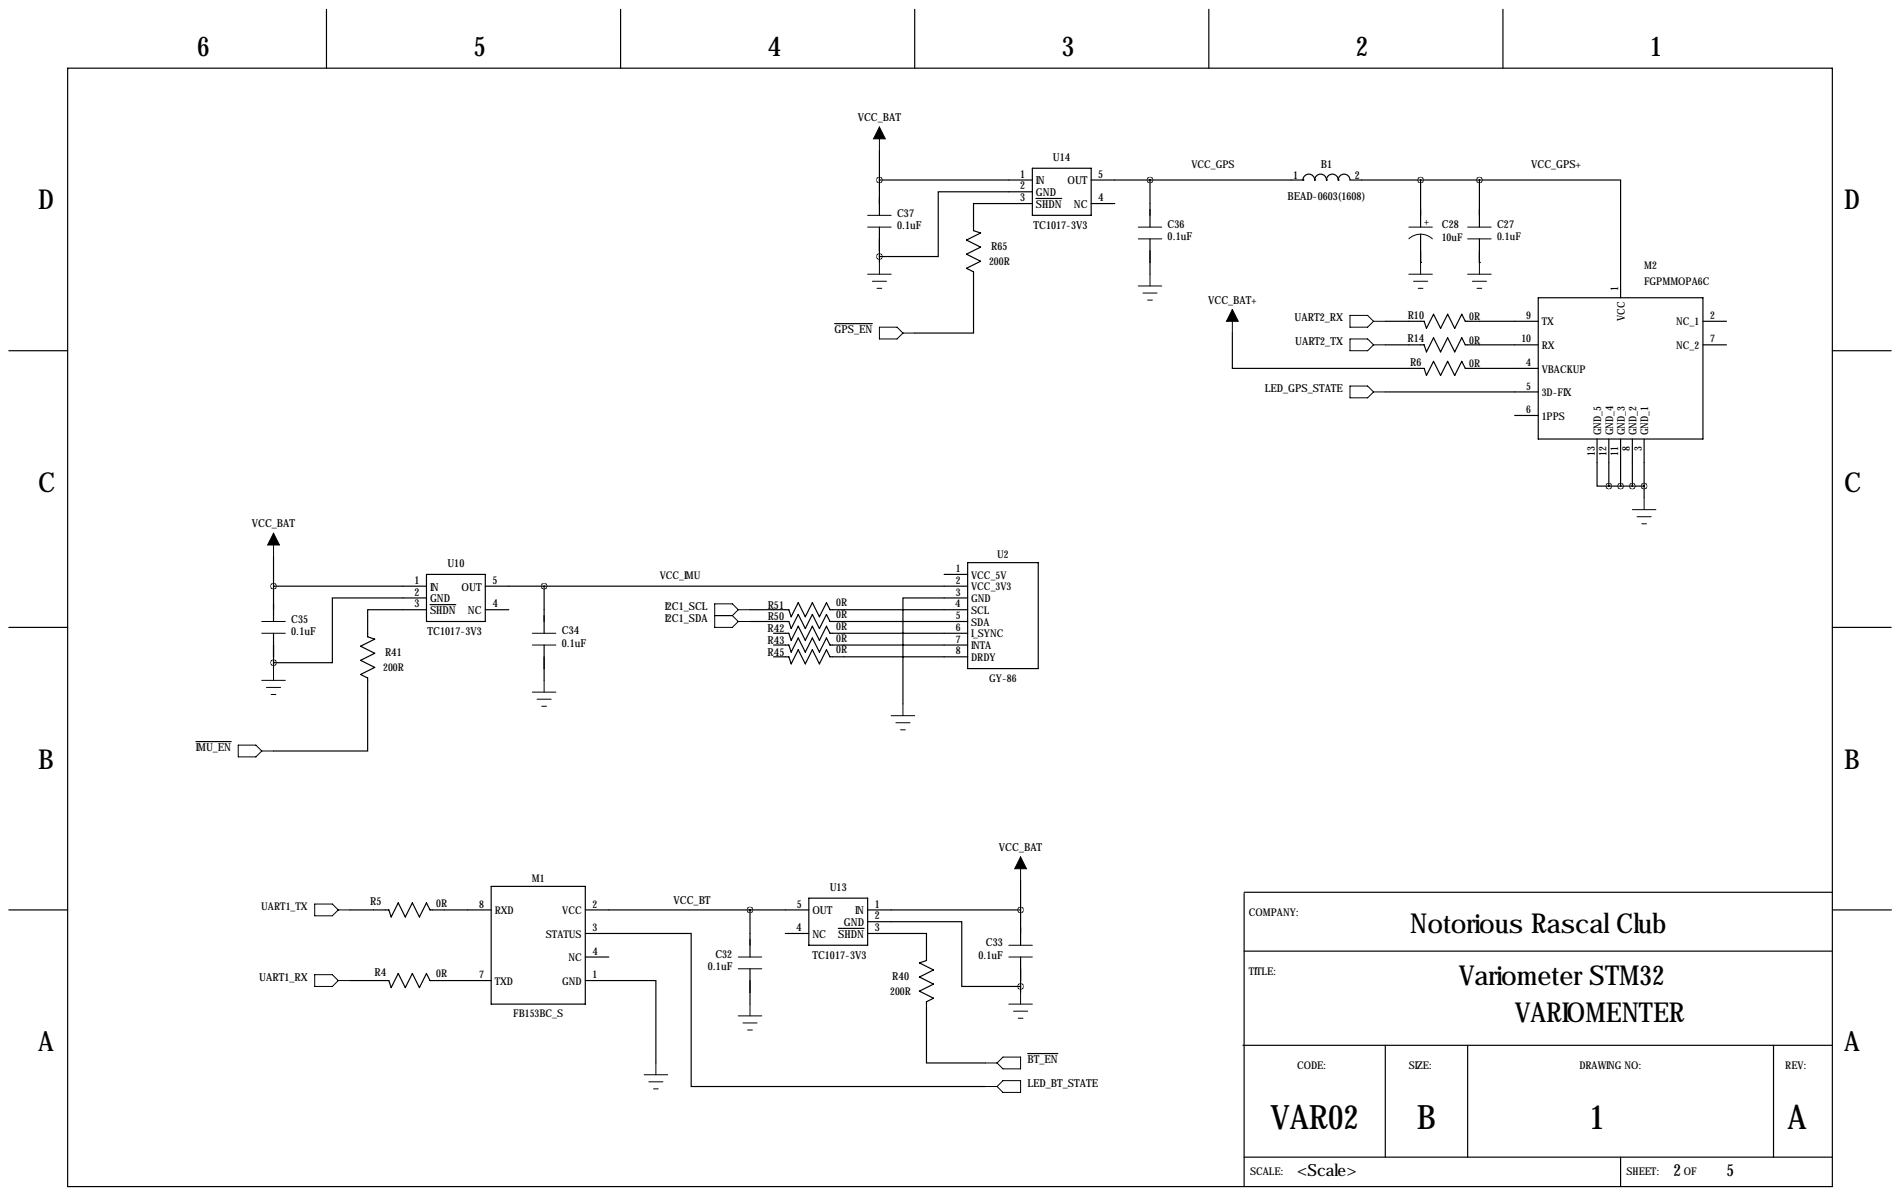
[picture p67: page 2]

CODE: VAR02 | SIZE: B | DRAWING NO: 1 | REV: A

<Scale> | 2 5

D

D

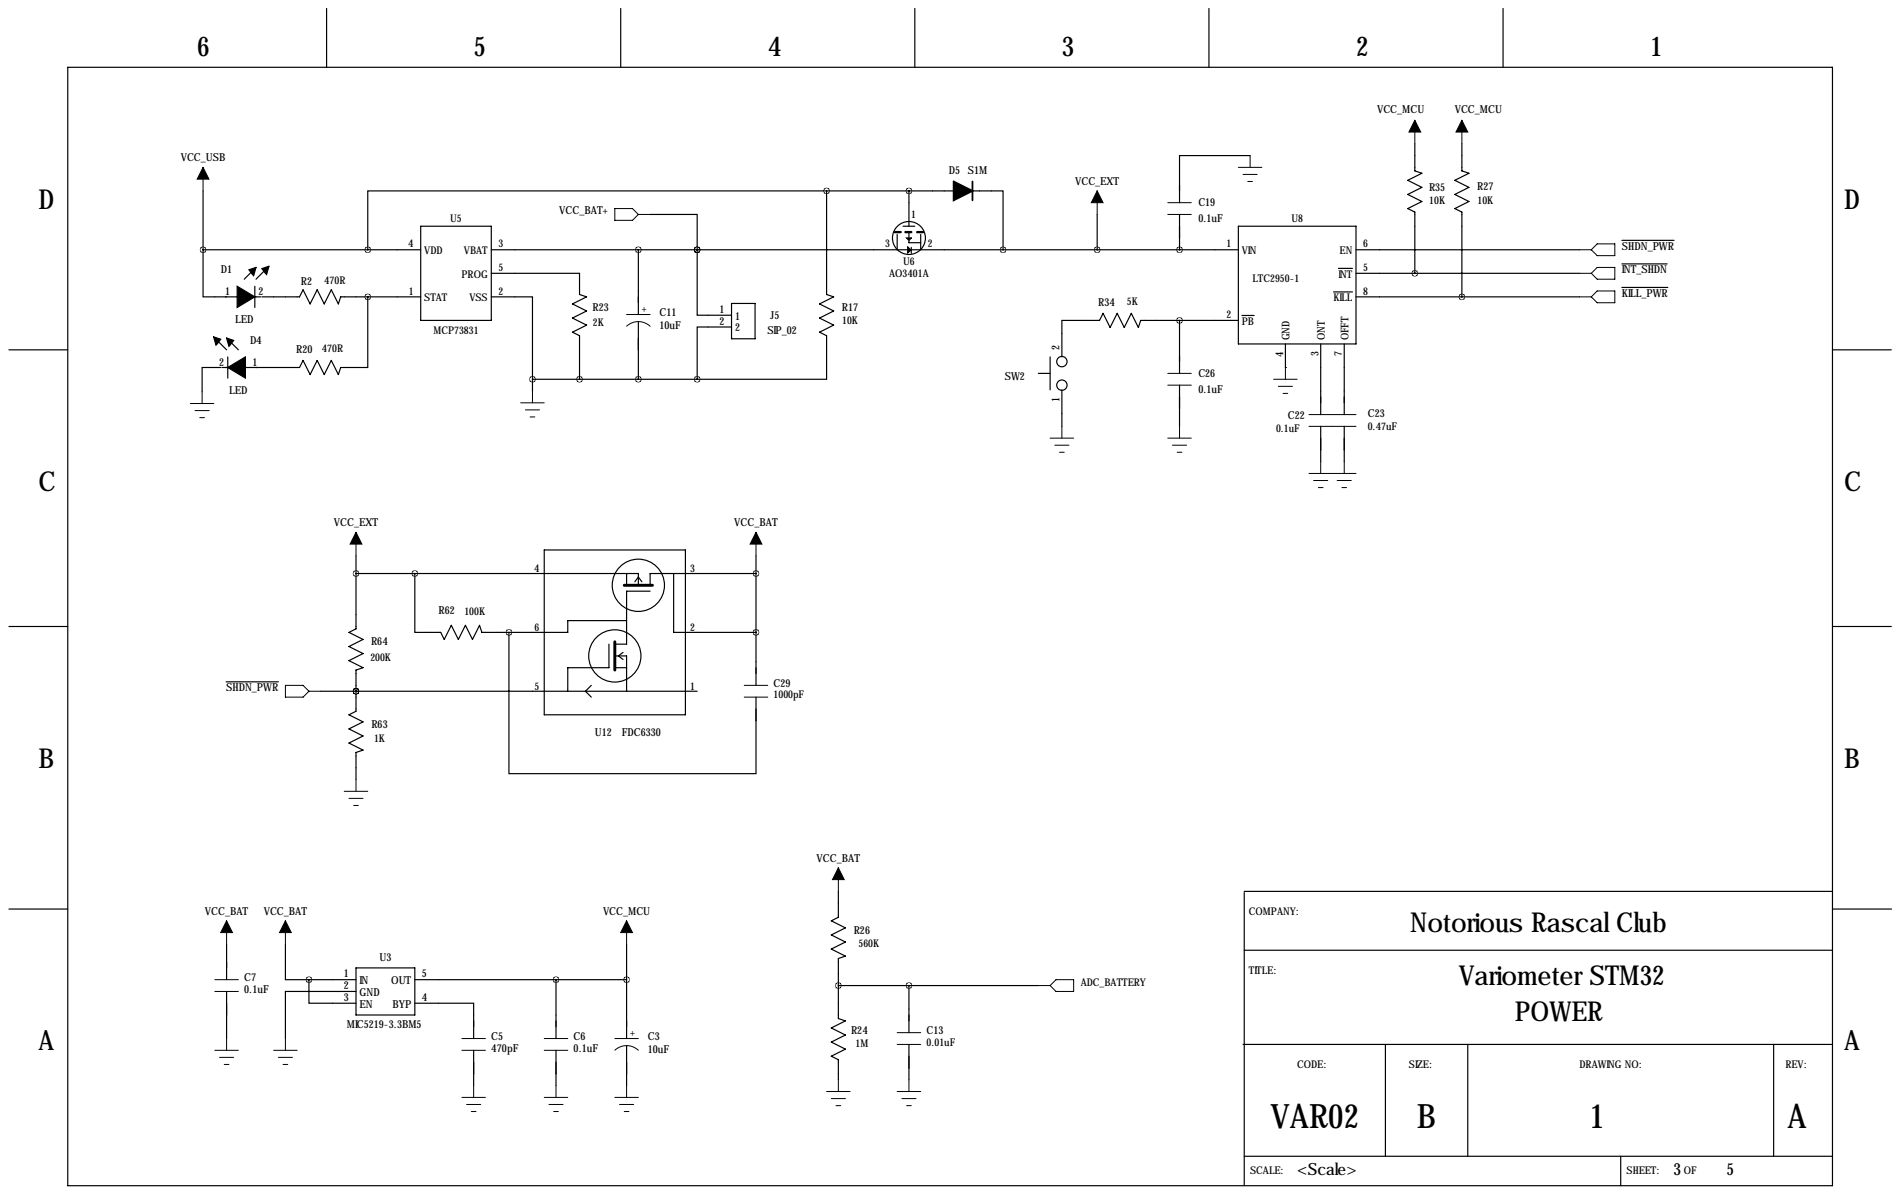
[picture p68: page 3]

IN 2 | 4
GND 3

CODE: VAR02 | SIZE: B | DRAWING NO: 1 | REV: A

<Scale> | 3 5

D

D

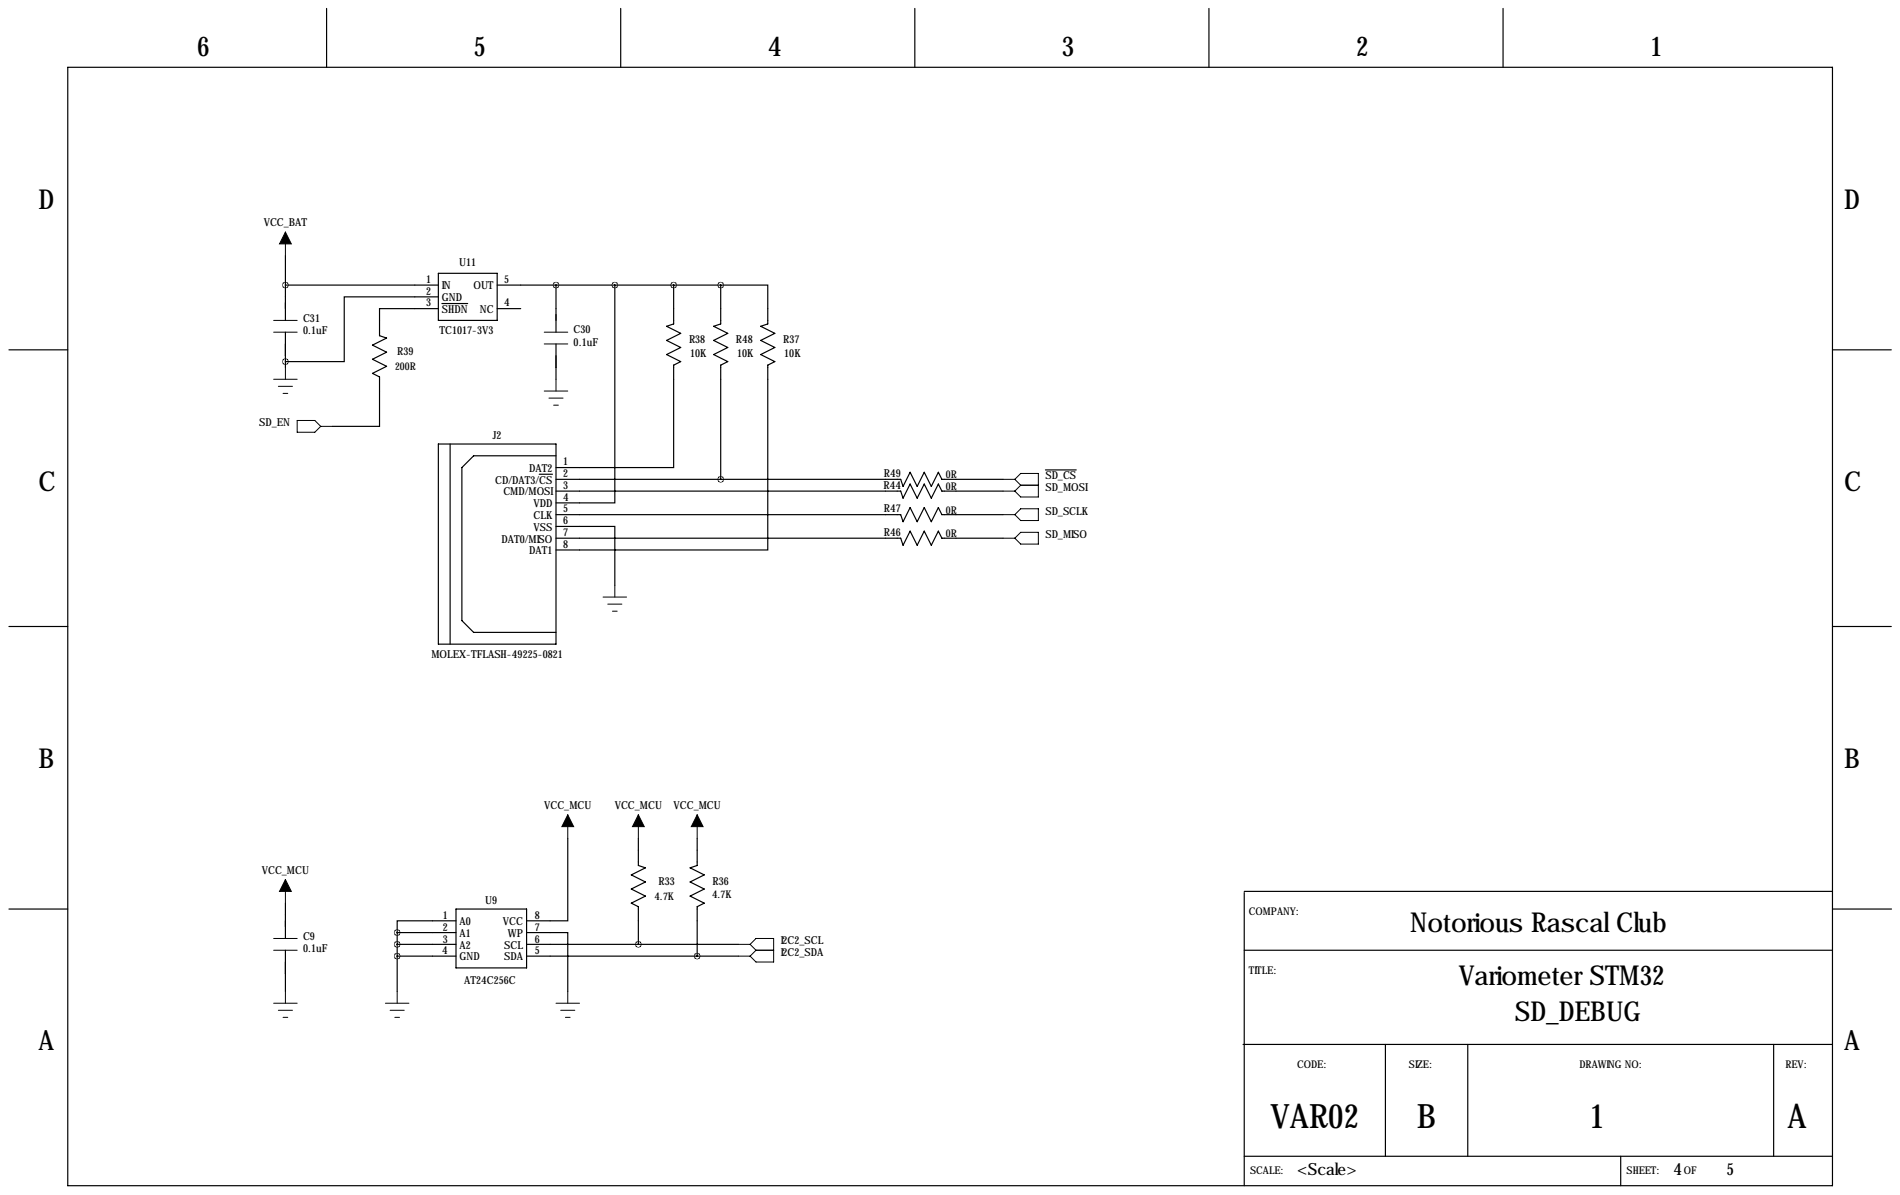
[picture p69: page 4]

CODE: VAR02 | SIZE: B | DRAWING NO: 1 | REV: A

<Scale> | 4 5

D

D

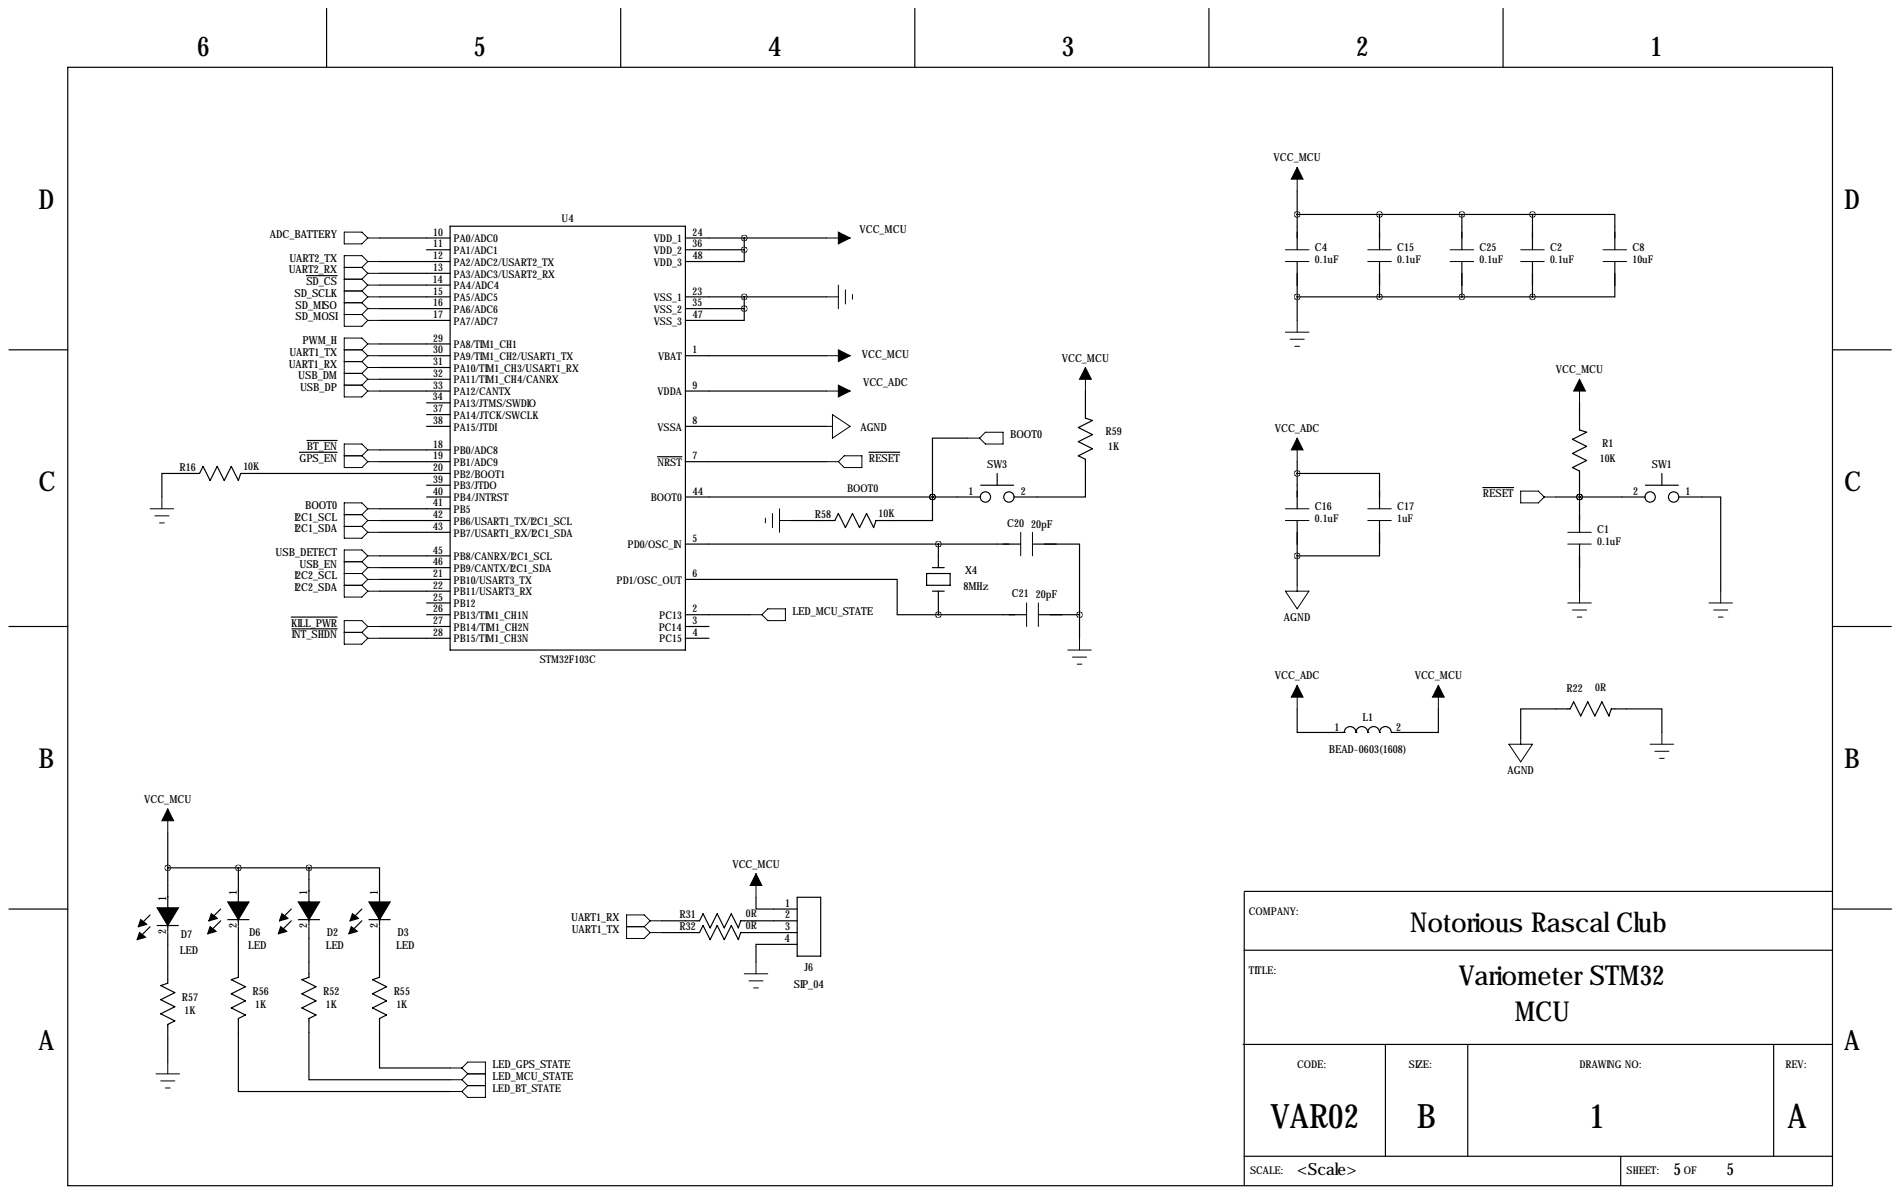
[picture p70: page 5]

CODE: VAR02 | SIZE: B | DRAWING NO: 1 | REV: A

<Scale> | 5 5
