akkdong/Vario-STM32/src/console/WConsole/WConsole/resource.h

//{{NO_DEPENDENCIES}}
// Microsoft Visual C++ generated include file.
// Used by wconsole.rc
//
#define IDD_WCONSOLE_DIALOG             102
#define IDR_MAINFRAME                   128
#define IDD_SELECT_PORT                 130
#define IDD_PREFERENCE_DIALOG           131
#define IDB_MATRIX_LARGE                133
#define IDB_MATRIX_SMALL                135
#define IDB_MATRIX_TINY                 136
#define IDC_GLIDER_TYPE                 1000
#define IDC_GLIDER_MANUFACTURE          1001
#define IDC_GLIDER_MODEL                1002
#define IDC_LOGGER_ENABLE               1003
#define IDC_LOGGER_TIMEZONE             1004
#define IDC_LOGGER_TAKEOFF_SPEED        1005
#define IDC_LOGGER_LANDING_TIMEOUT      1006
#define IDC_LOGGER_LOGGING_INTERVAL     1007
#define IDC_LOGGER_PILOT_NAME           1008
#define IDC_VARIO_SINK_THRESHOLD        1009
#define IDC_VARIO_CLIMB_THRESHOLD2      1010
#define IDC_VARIO_SENSITIVITY           1011
#define IDC_VARIO_SENTENCE              1012
#define IDC_VARIO_BARO_ONLY             1013
#define IDC_EDIT_TONE_TABLE             1014
#define IDC_VOLUME_VARIO                1015
#define IDC_VOLUME_EFFECT               1016
#define IDC_THRESHOLD_LOW_BATTERY       1017
#define IDC_THRESHOLD_SHUTDOWN_HOLDTIME 1018
#define IDC_KALMAN_VAR_ZMEAS            1020
#define IDC_KALMAN_VAR_ZACCEL           1021
#define IDC_KALMAN_VAR_ACCELBIAS        1022
#define IDC_CALDATA_ACCEL_X             1023
#define IDC_CALDATA_ACCEL_Y             1024
#define IDC_CALDATA_ACCEL_Z             1025
#define IDC_SAVE                        1029
#define IDC_RELOAD                      1032
#define IDC_STATIC_VOLUME_VARIO         1033
#define IDC_STATIC_VOLUME_EFFECT        1034
#define IDC_THRESHOLD_AUTO_POWEROFF_VARIO 1035
#define IDC_THRESHOLD_AUTO_POWEROFF_UMS 1036
#define IDC_CALDATA_GYRO_X              1037
#define IDC_CALDATA_GYRO_Y              1038
#define IDC_CALDATA_GYRO_Z              1039
#define IDC_SERIAL_PORT                 1040
#define IDC_SERIAL_BUADRATE             1046
#define IDC_SERIAL_DATABITS             1047
#define IDC_SERIAL_PARITY               1048
#define IDC_SERIAL_STOPBITS             1049
#define IDC_SERIAL_FLOWCONTROL          1050
#define IDC_CALIBRATION                 1051
#define IDC_SENSOR_VIEWER               1052
#define IDC_STORE                       1053
#define IDC_FACTORY_RESET               1054
#define IDC_CONNECT                     1055
#define IDC_LATITUDE                    1056
#define IDC_LONGITUDE                   1057
#define IDC_CONNECT2                    1058
#define IDC_PREFERENCES                 1058
#define IDC_SELECT_PORT                 5001
#define IDC_SEND_MESSAGE                5002

// Next default values for new objects
// 
#ifdef APSTUDIO_INVOKED
#ifndef APSTUDIO_READONLY_SYMBOLS
#define _APS_NEXT_RESOURCE_VALUE        137
#define _APS_NEXT_COMMAND_VALUE         32771
#define _APS_NEXT_CONTROL_VALUE         1057
#define _APS_NEXT_SYMED_VALUE           103
#endif
#endif
