akkdong/Vario-STM32/src-pio/UMS_mal.h

// USB_mal.h
//

#ifndef __USB_MAL_H__
#define __USB_MAL_H__

#include <Arduino.h>
#include "UsbMassStorage.h"


////////////////////////////////////////////////////////////////////////////////////
//

void usb_mal_init(uint32_t numberOfBlocks);



#endif // __USB_MAL_H__
