akkdong/Vario-STM32/src/console/WConsole/WConsole/VarioConsoleDlg.h

// VarioConsoleDlg.h : 헤더 파일
//

#pragma once
#include "afxcmn.h"
#include "SerialWnd.h"
#include "VarioSettings.h"
#include "MatrixStatic.h"
#include <list>

#define MAX_SERIAL_BUFFER			(1024)

#define TIMER_CHECK_RESPONSE		(0x1001)

// CVarioConsoleDlg 대화 상자
class CVarioConsoleDlg : public CDialogEx
{
// 생성입니다.
public:
	CVarioConsoleDlg(CWnd* pParent = NULL);	// 표준 생성자입니다.

// 대화 상자 데이터입니다.
#ifdef AFX_DESIGN_TIME
	enum { IDD = IDD_WCONSOLE_DIALOG };
#endif

protected:
	virtual void		DoDataExchange(CDataExchange* pDX);	// DDX/DDV 지원입니다.

private:
	void				ParseReceivedMessage();
	void				ProcessReceivedMessage(WORD code, UINT param, LPCTSTR lpszData);

	BOOL				UpdateData(BOOL bSaveAndValidate);
	void				UpdateTitle();

	void				OpenSerial(LPCTSTR lpszDevice, CSerial::EBaudrate, CSerial::EDataBits, CSerial::EParity, CSerial::EStopBits, CSerial::EHandshake);
	void				CloseSerial();

// 구현입니다.
protected:
	//
	HICON				m_hIcon;

	//
	CSerialWnd			m_Serial;
	BOOL				m_bConnected;

	CHAR				m_pSerialBuf[MAX_SERIAL_BUFFER];
	int					m_nBufLen;

	std::list<CString>	m_RecvMsgs;
	std::list<CString>	m_SendMsgs;
	BOOL				m_bRecvVarioMsg;

	//
	UINT				m_nTimerID;

	// Serial Settings
	int					m_nPortNum;
	CSerial::EBaudrate	m_nBaudRate;
	CSerial::EDataBits	m_nDataBits;
	CSerial::EParity	m_nParity;
	CSerial::EStopBits	m_nStopBits;

	//
	CMatrixStatic		m_wndLatitude;
	CMatrixStatic		m_wndLongitude;

	CString				m_strLatitude;
	CString				m_strLongitude;


protected:
	// 생성된 메시지 맵 함수
	virtual BOOL		OnInitDialog();
	virtual void		OnOK();
	virtual void		OnCancel();

	afx_msg void		OnPaint();
	afx_msg HCURSOR		OnQueryDragIcon();
	afx_msg void		OnTimer(UINT nIDEvent);
	afx_msg LRESULT		OnSerialMessage(WPARAM, LPARAM);
	afx_msg void		OnEditToneTable();
	afx_msg void		OnCalibration();
	afx_msg void		OnViewSensorData();
	afx_msg void		OnConnect();
	afx_msg void		OnReload();
	afx_msg void		OnPreferences();
	afx_msg void		OnSelectPort();
	afx_msg void		OnSendMessage();

	DECLARE_MESSAGE_MAP()

};
