akkdong/Vario-STM32/src/bootloader-serial/programmer/programmer-ui/MemoryDumpDlg.h

#pragma once

#include "HexEdit.h"
#include "Packet.h"

////////////////////////////////////////////////////////////////////////////////////
//

class CDownloaderDlg;


////////////////////////////////////////////////////////////////////////////////////
//

class CMemoryDumpDlg : public CDialogEx, protected BPacketListener
{
public:
	CMemoryDumpDlg(CDownloaderDlg * pParent);
	~CMemoryDumpDlg();

	// 대화 상자 데이터입니다.
#ifdef AFX_DESIGN_TIME
	enum { IDD = IDD_MEMORY_DUMP };
#endif

protected:
	virtual void		DoDataExchange(CDataExchange* pDX);    // DDX/DDV 지원입니다.
	virtual void		OnBPacketReceived(BPacket * pPacket);

	BOOL				UpdateData(BOOL bSaveAndValidate = TRUE);

private:
	void				RequestMemory(uint32_t address, uint16_t size);
	void				RequestMemory();

	void				EnableControls(BOOL bEnable);

protected:
	//
	UINT				m_nTimerID;

	CComboBox			m_wndAddress;
	CString				m_strAddress;
	CEdit				m_wndSize;
	CString				m_strSize;
	CHexEdit			m_wndHexEdit;

	//
	uint32_t			m_nAddress;
	uint16_t			m_nReadSize;

	uint32_t			m_nAddrRead;

	//
	CDownloaderDlg *	m_pDlgMain;

protected:
	virtual BOOL		OnInitDialog();
	virtual void		OnOK();
	virtual void		OnCancel();

	afx_msg void		OnTimer(UINT nIDEvent);
	afx_msg void		OnKillFocusAddress();
	afx_msg void		OnKillFocusSize();

	afx_msg void		OnSave();

	DECLARE_MESSAGE_MAP()
};
