akkdong/Vario-STM32/src/bootloader-serial/programmer/programmer-ui/resource.h

//{{NO_DEPENDENCIES}}
// Microsoft Visual C++ generated include file.
// Used by programmer-ui.rc
//
#define IDM_ABOUTBOX                    0x0010
#define IDD_ABOUTBOX                    100
#define IDS_ABOUTBOX                    101
#define IDR_MAINFRAME                   128
#define IDD_SELECT_PORT                 130
#define IDD_DOWNLOADER                  133
#define IDD_MEMORY_DUMP                 135
#define IDR_HEXCTRLMENU                 138
#define IDD_PROGRAM                     139
#define IDD_UPLOAD                      140
#define IDC_SERIAL_PORT                 1000
#define IDC_SERIAL_BUADRATE             1001
#define IDC_SERIAL_DATABITS             1002
#define IDC_SERIAL_PARITY               1003
#define IDC_SERIAL_STOPBITS             1004
#define IDC_SERIAL_FLOWCONTROL          1005
#define IDC_CONNECT                     1005
#define IDC_FILE_PATH                   1006
#define IDC_BROWSE                      1007
#define IDC_SERIAL_HANDSHAKE            1007
#define IDC_IDENTIFY                    1009
#define IDC_ERASE                       1010
#define IDC_DOWNLOAD                    1010
#define IDC_ERASE_ALL                   1011
#define IDC_UPLOAD                      1011
#define IDC_READ_MEMORY                 1012
#define IDC_DEV_ID                      1012
#define IDC_WRITE_MEMORY                1013
#define IDC_FW_VER                      1013
#define IDC_RESET_DEVICE                1014
#define IDC_BOOT_VER                    1014
#define IDC_START_USERAPP               1015
#define IDC_MEMORY                      1015
#define IDC_REPORT_LIST                 1017
#define IDC_HEXEDIT                     1018
#define IDC_MEMORY_SIZE                 1020
#define IDC_READ                        1021
#define IDC_ADDRESS                     1022
#define IDC_TEST                        1023
#define IDC_LOG_CLEAR                   1023
#define IDC_TEST2                       1024
#define IDC_RUN_USERPROG                1024
#define IDC_VERIFY_PROGRAM              1027
#define IDC_RUN_PROGRAM                 1028
#define IDC_START                       1029
#define IDCAN                           1030
#define IDC_LOG_HISTORY                 1031
#define IDC_LOG_DETAIL                  1032
#define IDC_REFRESH                     1034
#define IDC_SERIAL_BAUDRATE             1035
#define IDC_SAVE                        1035
#define IDC_BUTTON1                     1036
#define IDC_DEV_CHECK                   1036
#define IDC_EXECUTE                     8000
#define ID_EDIT_DELETE                  32771

// Next default values for new objects
// 
#ifdef APSTUDIO_INVOKED
#ifndef APSTUDIO_READONLY_SYMBOLS
#define _APS_NEXT_RESOURCE_VALUE        143
#define _APS_NEXT_COMMAND_VALUE         32772
#define _APS_NEXT_CONTROL_VALUE         1037
#define _APS_NEXT_SYMED_VALUE           103
#endif
#endif
