akkdong/Vario-STM32/src/bootloader-serial/programmer/programmer-console/Util.h

#pragma once

#include <stdint.h>

////////////////////////////////////////////////////////////////////////////////////
//

char     cpu_le();

uint32_t be_u32(const uint32_t v);
uint32_t le_u32(const uint32_t v);
