akkdong/Vario-STM32/src/bootloader-serial/programmer/programmer-console/stdafx.h

// stdafx.h : 자주 사용하지만 자주 변경되지는 않는
// 표준 시스템 포함 파일 또는 프로젝트 관련 포함 파일이
// 들어 있는 포함 파일입니다.
//

#pragma once

#include "targetver.h"

#include <tchar.h>

#include <sys/types.h>
#include <sys/stat.h>  
#include <sys/locking.h> 
#include <fcntl.h>
#include <stdlib.h>
#include <stdint.h>
#include <stdio.h>
#include <string.h>
#include <io.h>

#include <windows.h>
